himikat123/Weather-monitor-BIM32/display Nextion/img/background.png

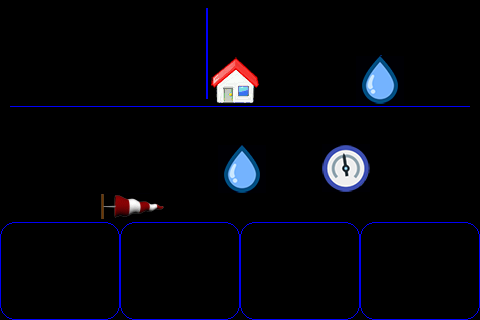
display Nextion/img/background.png
