himikat123/Weather-monitor-BIM32/display Nextion/img/clock.png

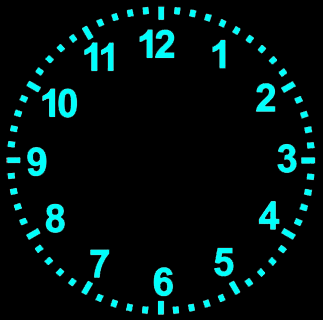
display Nextion/img/clock.png
