himikat123/Weather-monitor-BIM32/enclosure/BME680 enclosure/BME680_1.jpg

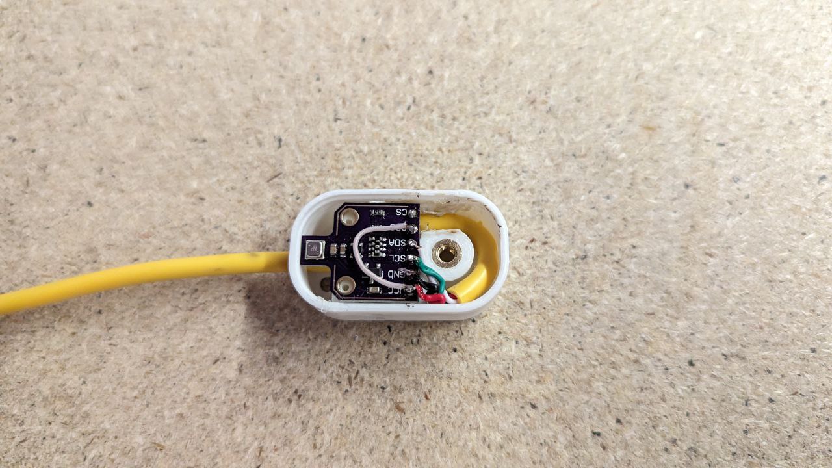
enclosure/BME680 enclosure/BME680_1.jpg
