himikat123/Weather-monitor-BIM32/enclosure/BME680 enclosure/STL/BME680_main.png

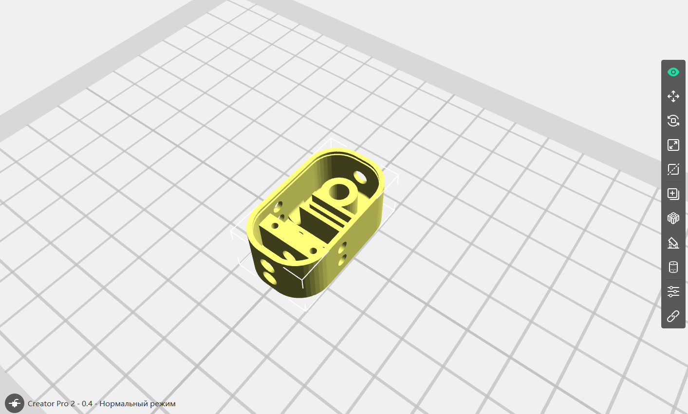
enclosure/BME680 enclosure/STL/BME680_main.png
