himikat123/Weather-monitor-BIM32/enclosure/Solidworks2023/buttons/alarm/alarm_button.png

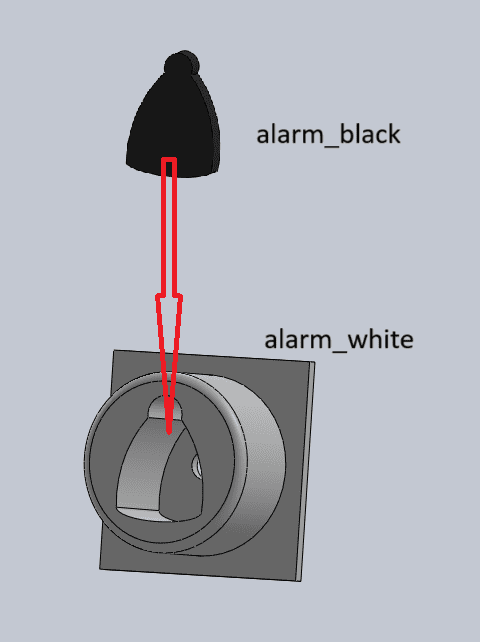
enclosure/Solidworks2023/buttons/alarm/alarm_button.png
