himikat123/Weather-monitor-BIM32/enclosure/Solidworks2023/buttons/display_1/disp1_button.png

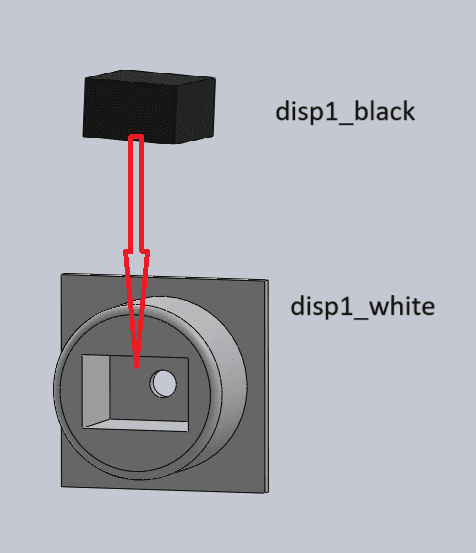
enclosure/Solidworks2023/buttons/display_1/disp1_button.png
