himikat123/Weather-monitor-BIM32/enclosure/Solidworks2023/buttons/display_2/disp2_button.png

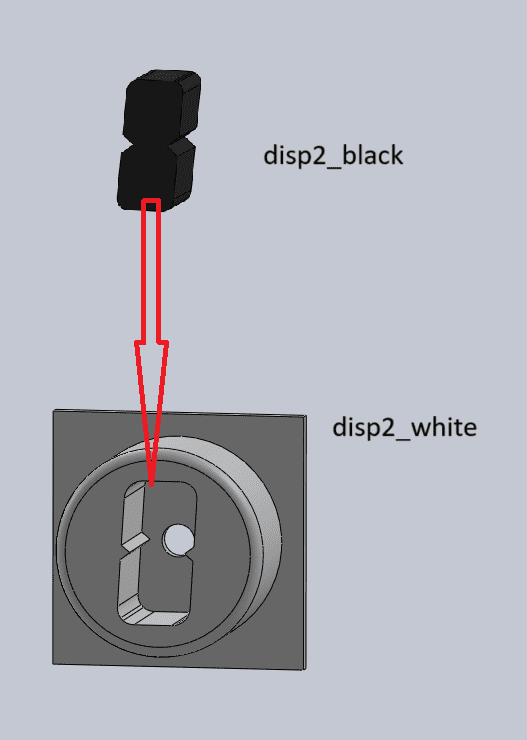
enclosure/Solidworks2023/buttons/display_2/disp2_button.png
