himikat123/Weather-monitor-BIM32/enclosure/Solidworks2023/buttons/reset/reset_button.png

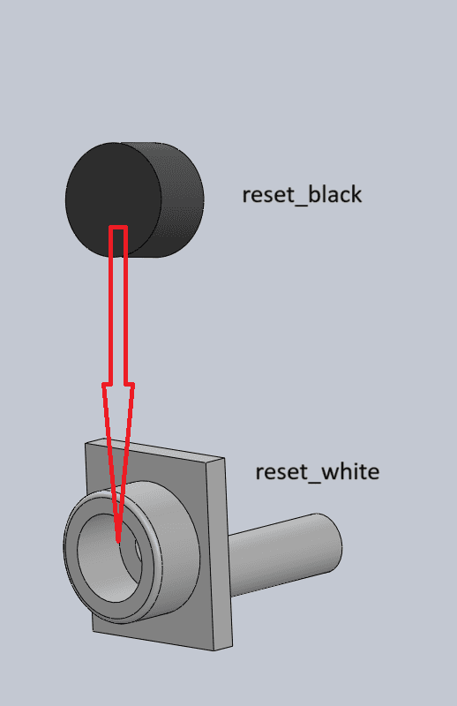
enclosure/Solidworks2023/buttons/reset/reset_button.png
