himikat123/Weather-monitor-BIM32/enclosure/Solidworks2023/buttons/settings/settings_button.png

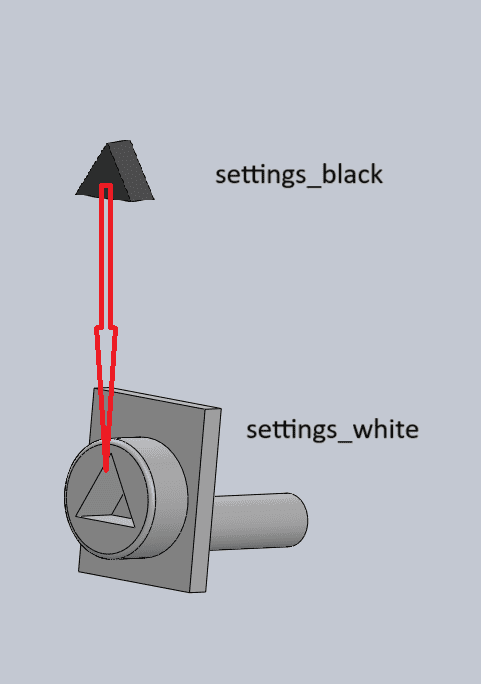
enclosure/Solidworks2023/buttons/settings/settings_button.png
