himikat123/Weather-monitor-BIM32/enclosure/Solidworks2023/clipSpeakerConnector.png

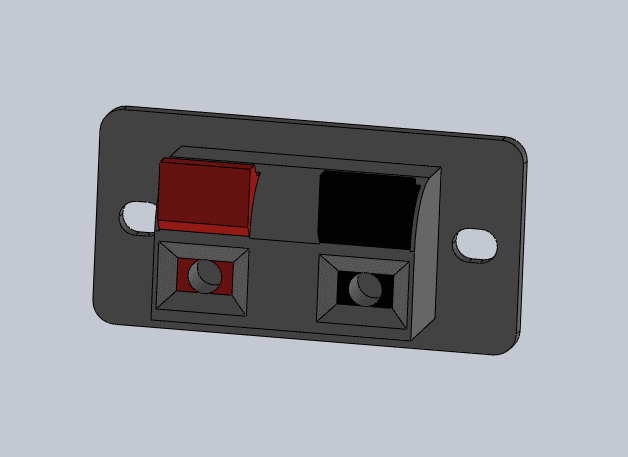
enclosure/Solidworks2023/clipSpeakerConnector.png
