himikat123/Weather-monitor-BIM32/enclosure/Solidworks2023/cover/cover.png

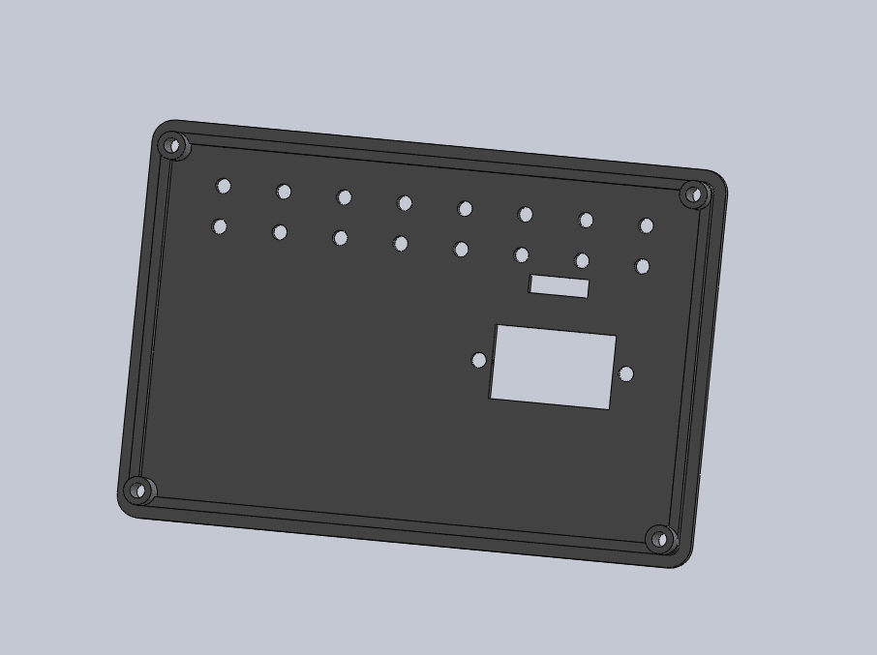
enclosure/Solidworks2023/cover/cover.png
