himikat123/Weather-monitor-BIM32/enclosure/Solidworks2023/display/display.png

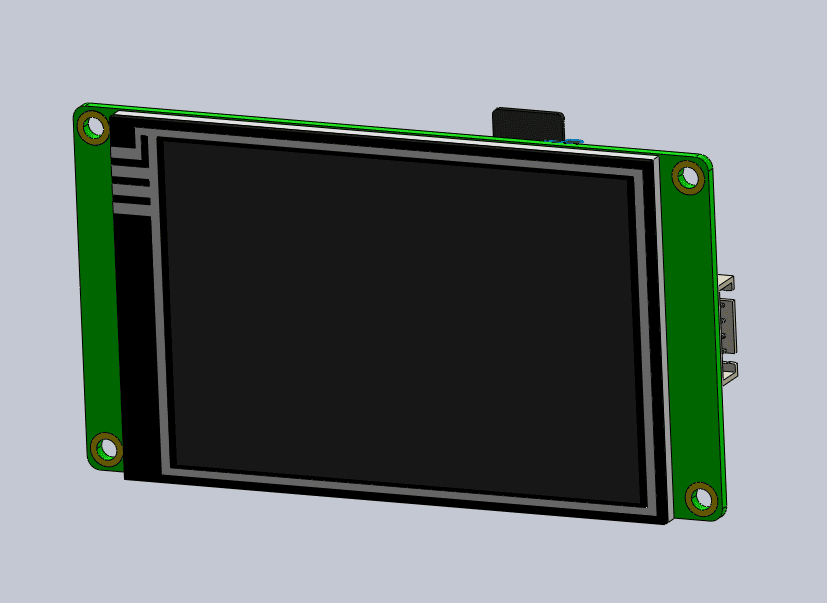
enclosure/Solidworks2023/display/display.png
