himikat123/Weather-monitor-BIM32/enclosure/Solidworks2023/face/face.png

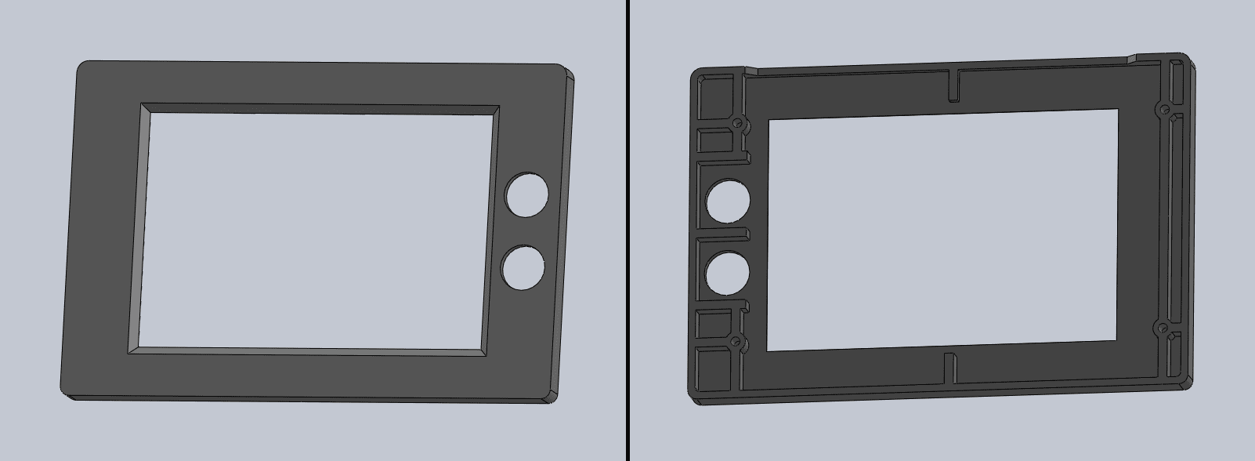
enclosure/Solidworks2023/face/face.png
