himikat123/Weather-monitor-BIM32/enclosure/Solidworks2023/frame/frame.png

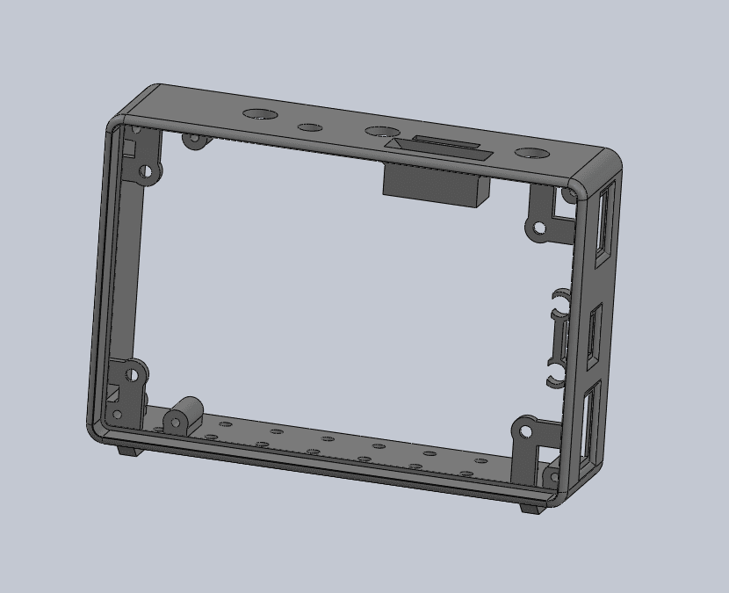
enclosure/Solidworks2023/frame/frame.png
