himikat123/Weather-monitor-BIM32/enclosure/Solidworks2023/lid/lid.png

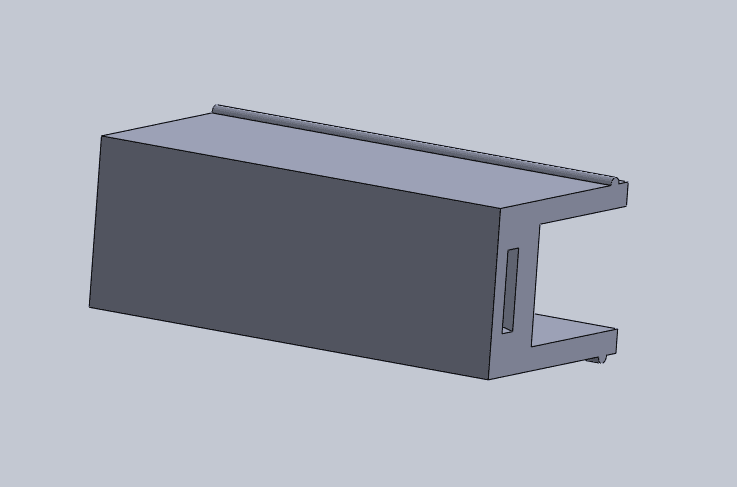
enclosure/Solidworks2023/lid/lid.png
