himikat123/Weather-monitor-BIM32/enclosure/Solidworks2023/pcb/pcb.png

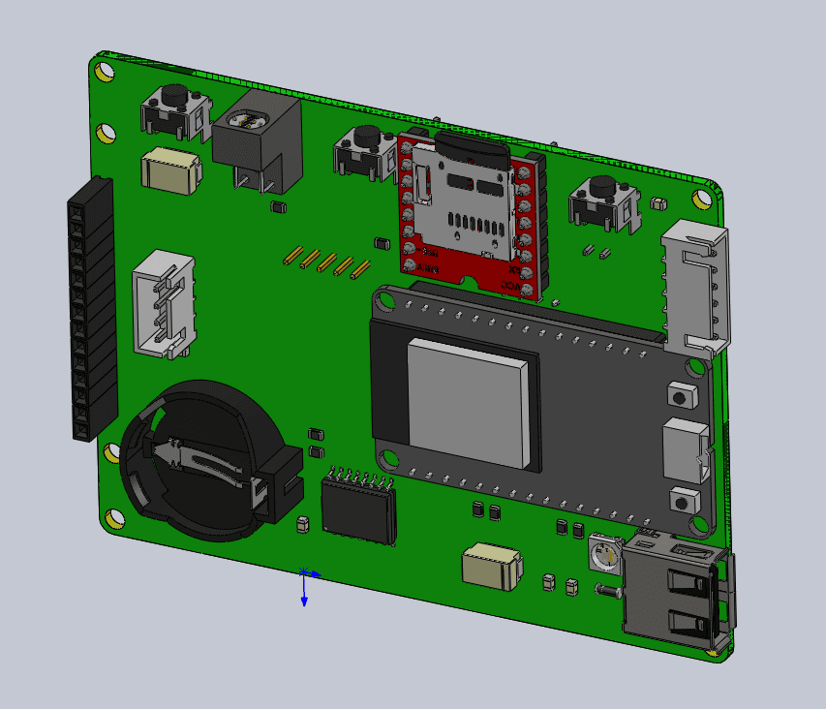
enclosure/Solidworks2023/pcb/pcb.png
