himikat123/Weather-monitor-BIM32/enclosure/Solidworks2023/photoresistor/photoresistor.png

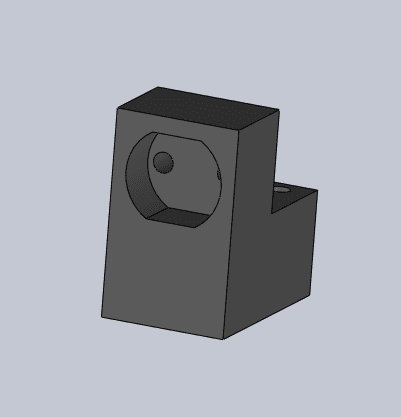
enclosure/Solidworks2023/photoresistor/photoresistor.png
