himikat123/Weather-monitor-BIM32/enclosure/Solidworks2023/screw1.png

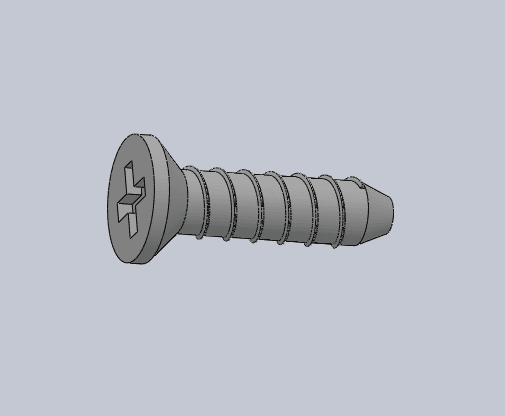
enclosure/Solidworks2023/screw1.png
