himikat123/Weather-monitor-BIM32/enclosure/Solidworks2023/screw2.png

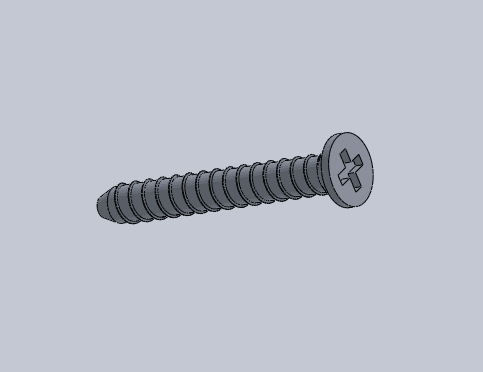
enclosure/Solidworks2023/screw2.png
