himikat123/Weather-monitor-BIM32/enclosure/Solidworks2023/speaker.png

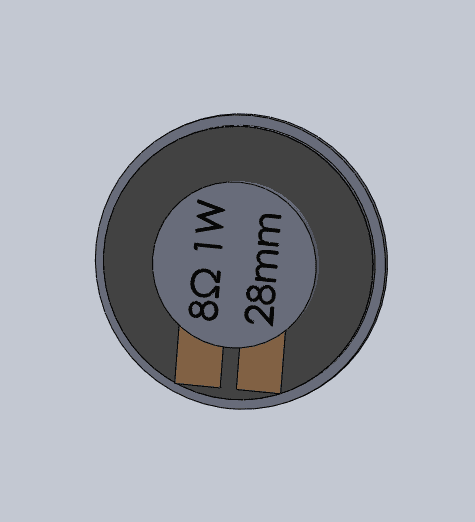
enclosure/Solidworks2023/speaker.png
