himikat123/Weather-monitor-BIM32/enclosure/STL/buttons/alarm/alarm_black.png

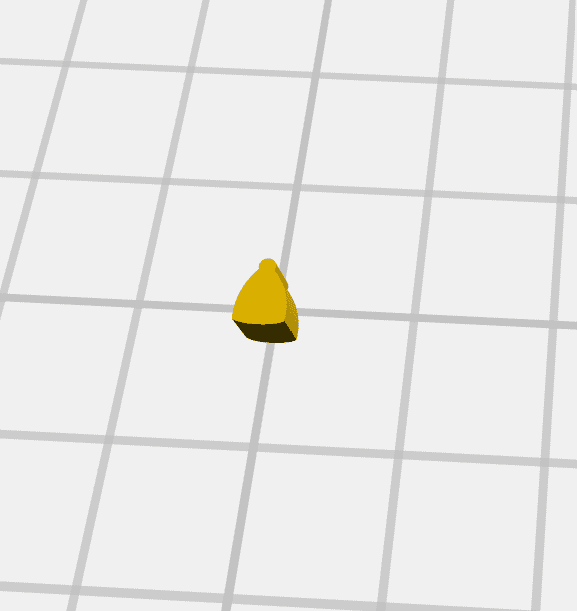
enclosure/STL/buttons/alarm/alarm_black.png
