himikat123/Weather-monitor-BIM32/enclosure/STL/buttons/alarm/alarm_white.png

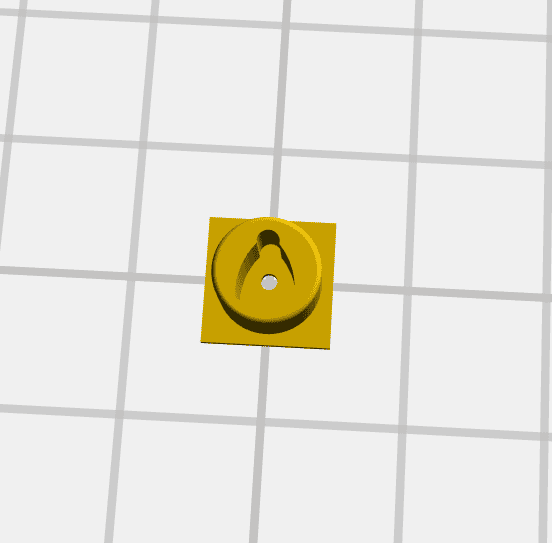
enclosure/STL/buttons/alarm/alarm_white.png
