himikat123/Weather-monitor-BIM32/enclosure/STL/buttons/display_1/disp1_black.png

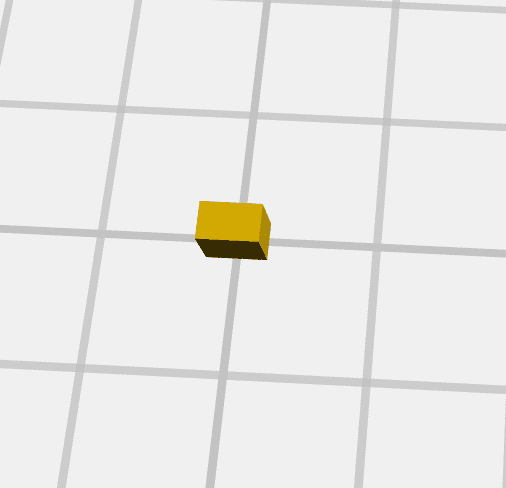
enclosure/STL/buttons/display_1/disp1_black.png
