himikat123/Weather-monitor-BIM32/enclosure/STL/buttons/display_2/disp2_black.png

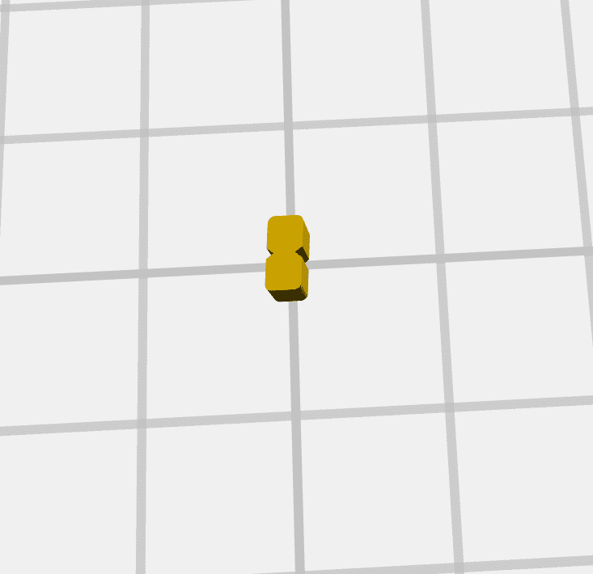
enclosure/STL/buttons/display_2/disp2_black.png
