himikat123/Weather-monitor-BIM32/enclosure/STL/buttons/reset/reset_black.png

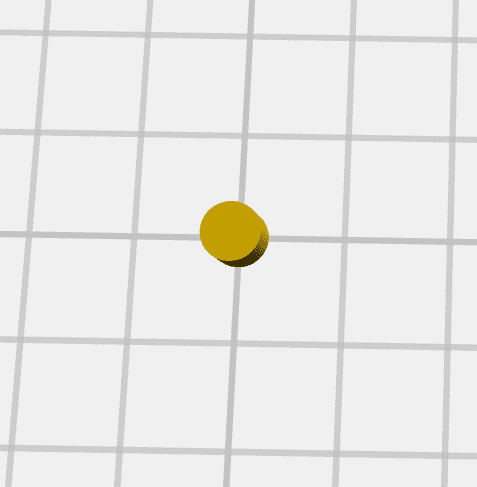
enclosure/STL/buttons/reset/reset_black.png
