himikat123/Weather-monitor-BIM32/enclosure/STL/buttons/reset/reset_white.png

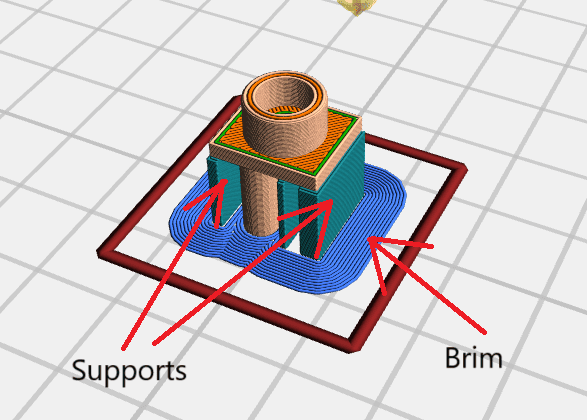
enclosure/STL/buttons/reset/reset_white.png
