himikat123/Weather-monitor-BIM32/enclosure/STL/buttons/settings/setiings_black.png

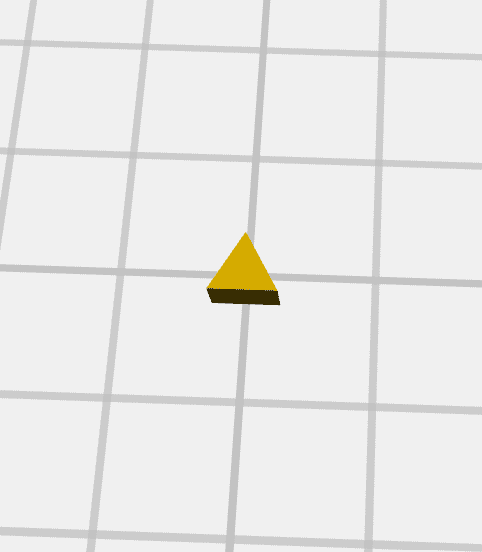
enclosure/STL/buttons/settings/setiings_black.png
