himikat123/Weather-monitor-BIM32/enclosure/STL/buttons/settings/setiings_white.png

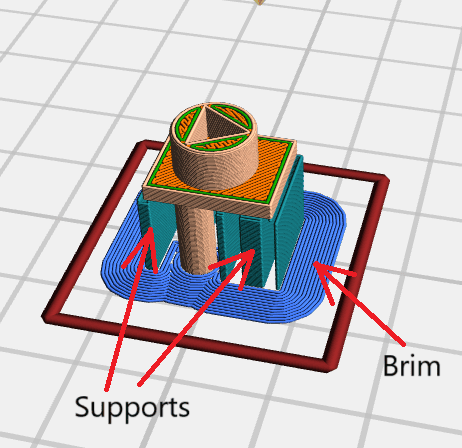
enclosure/STL/buttons/settings/setiings_white.png
