himikat123/Weather-monitor-BIM32/enclosure/STL/cover/cover_with_clip.png

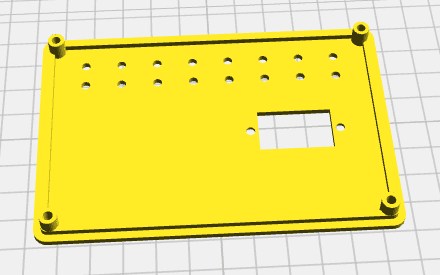
enclosure/STL/cover/cover_with_clip.png
