himikat123/Weather-monitor-BIM32/enclosure/STL/face/face.png

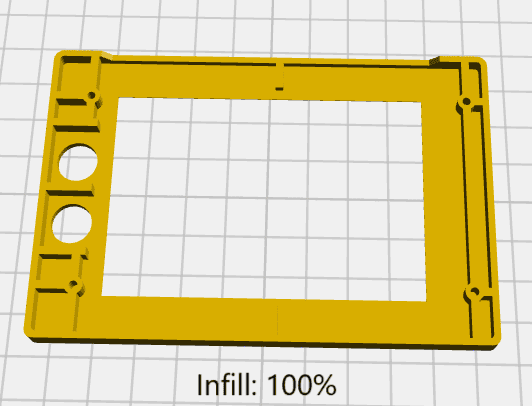
enclosure/STL/face/face.png
