himikat123/Weather-monitor-BIM32/enclosure/STL/face/face_wo_button_holes.png

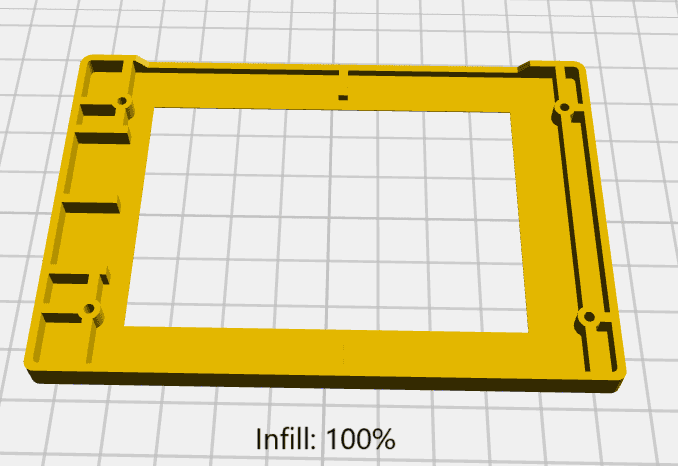
enclosure/STL/face/face_wo_button_holes.png
