himikat123/Weather-monitor-BIM32/enclosure/STL/frame/frame.png

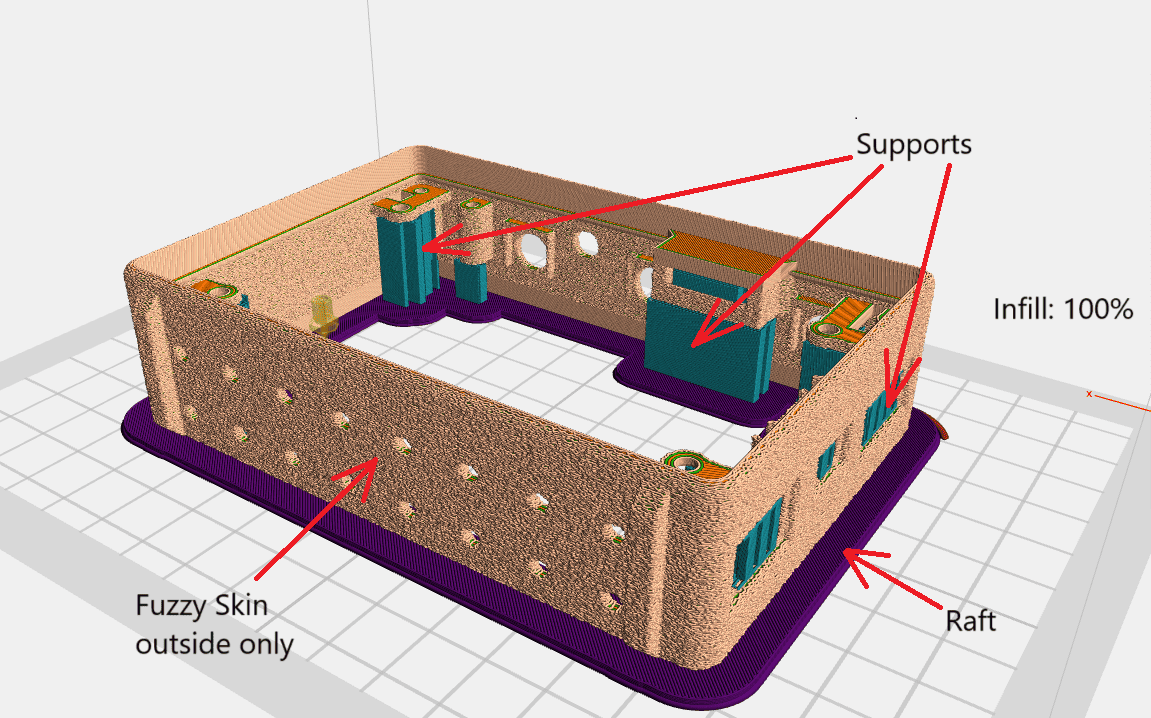
enclosure/STL/frame/frame.png
