himikat123/Weather-monitor-BIM32/enclosure/STL/frame/frame_with_4_pin_sensors_connector.png

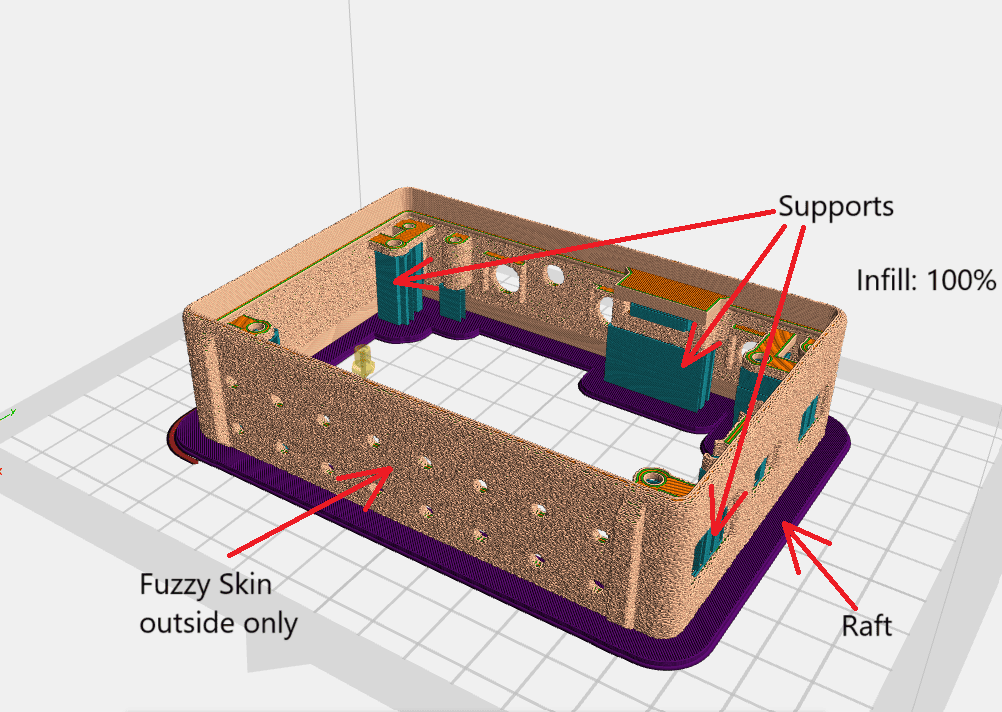
enclosure/STL/frame/frame_with_4_pin_sensors_connector.png
