himikat123/Weather-monitor-BIM32/enclosure/STL/frame/frame_wo_light_sensor_hole.png

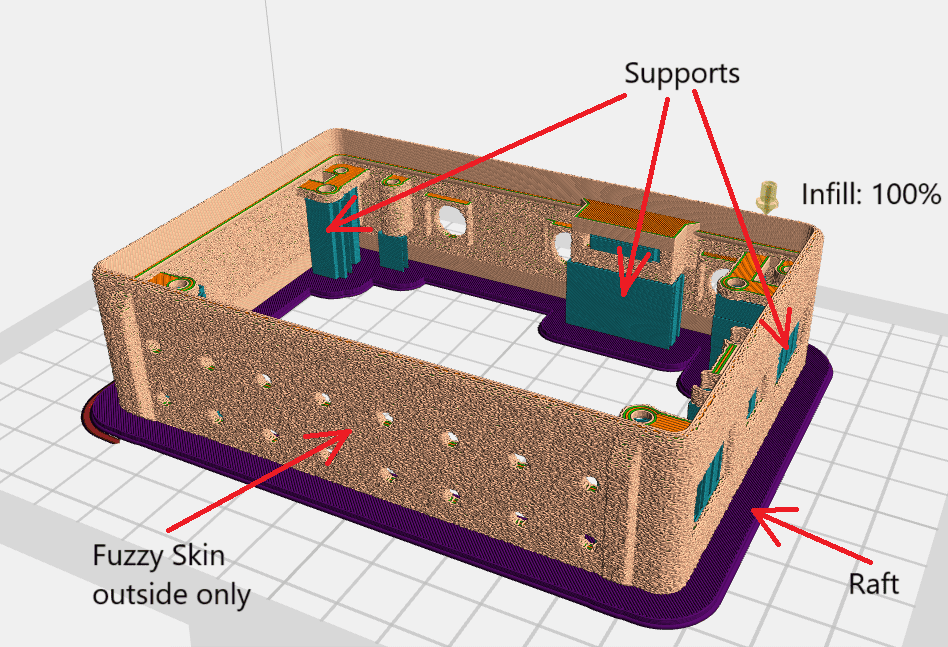
enclosure/STL/frame/frame_wo_light_sensor_hole.png
