himikat123/Weather-monitor-BIM32/enclosure/STL/frame/frame_wo_top_buttons_holes.png

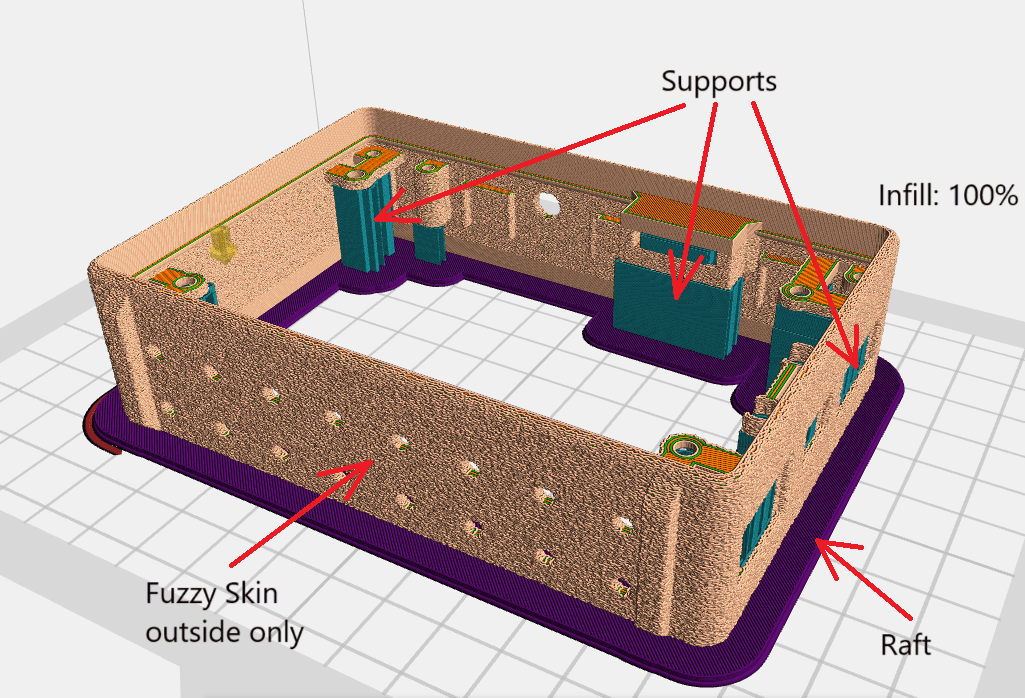
enclosure/STL/frame/frame_wo_top_buttons_holes.png
