himikat123/Weather-monitor-BIM32/enclosure/STL/lid/lid.png

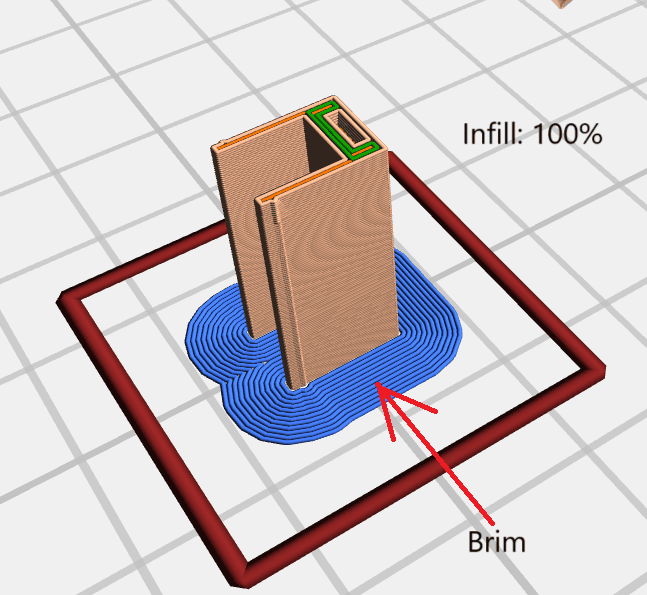
enclosure/STL/lid/lid.png
