himikat123/Weather-monitor-BIM32/enclosure/STL/photoresistor/photoresistor.png

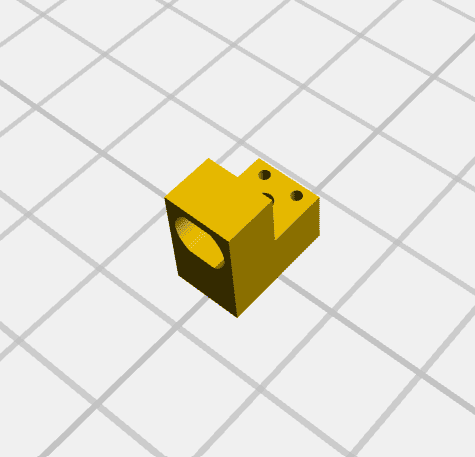
enclosure/STL/photoresistor/photoresistor.png
