himikat123/Weather-monitor-BIM32/img/aboutRU.png

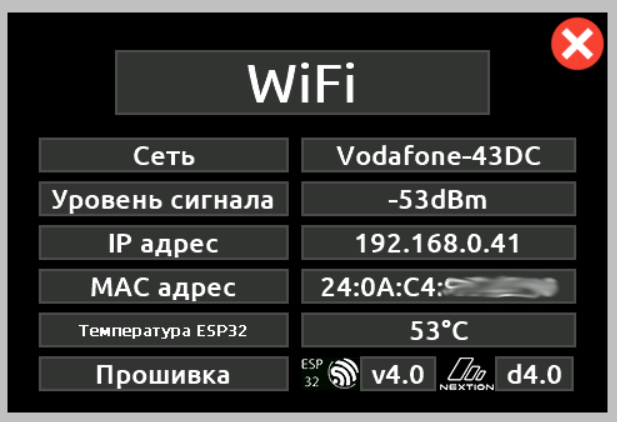
img/aboutRU.png
