himikat123/Weather-monitor-BIM32/img/device1_RU.jpg

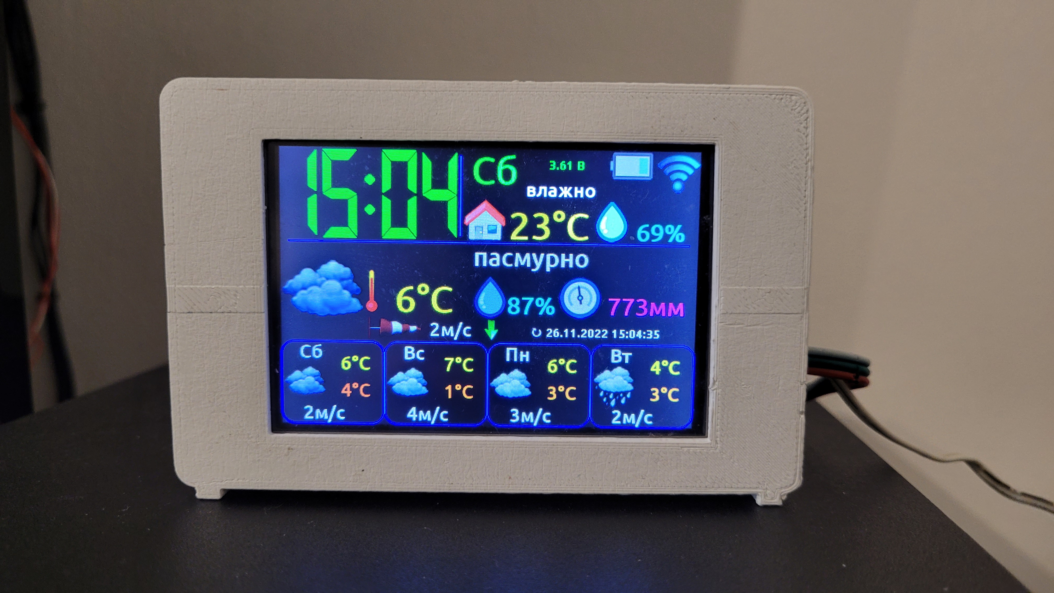
img/device1_RU.jpg
