himikat123/Weather-monitor-BIM32/img/f6_ru.jpg

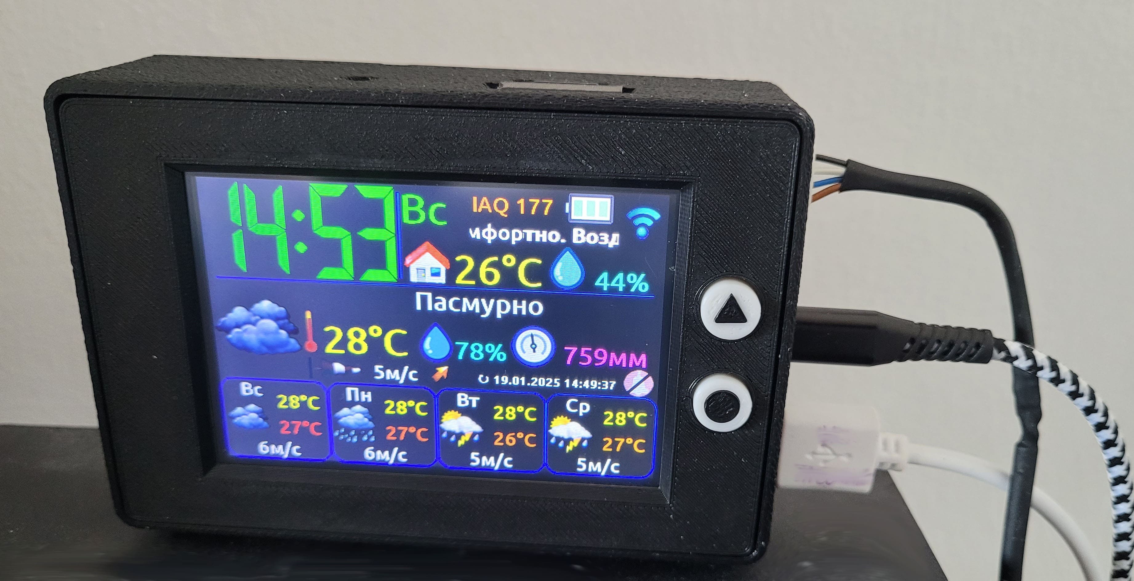
img/f6_ru.jpg
