himikat123/Weather-monitor-BIM32/img/mainRU.gif

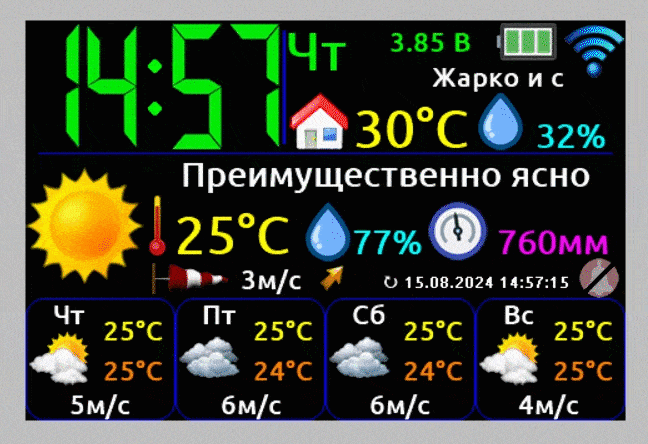
img/mainRU.gif
