himikat123/Weather-monitor-BIM32/PCB/diptrace/BIM32.png

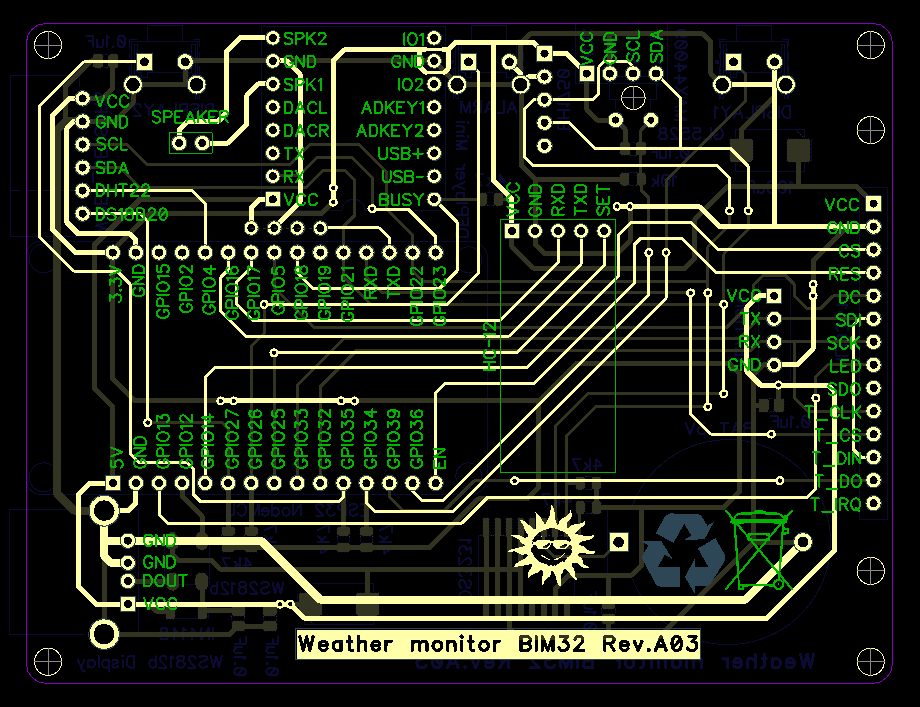
PCB/diptrace/BIM32.png
