himikat123/Weather-monitor-BIM32/PCB/diptrace/Version.png

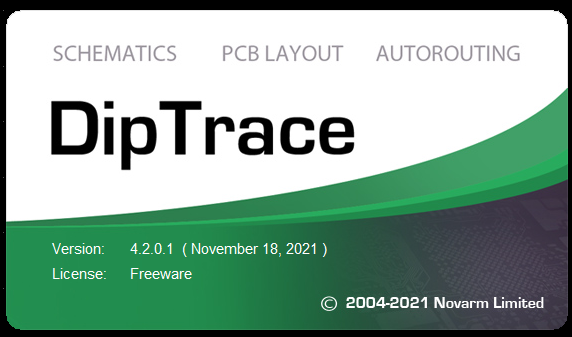
PCB/diptrace/Version.png
