himikat123/Weather-monitor-BIM32/PCB/PCB Bottom.png

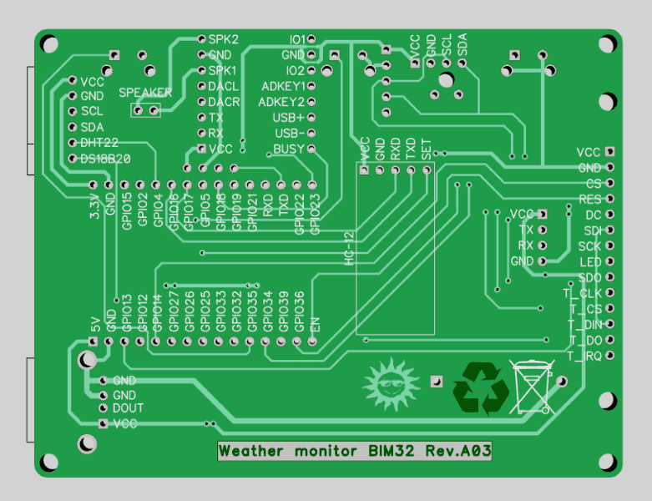
PCB/PCB Bottom.png
