himikat123/Weather-monitor-BIM32/PCB/PCB Top.png

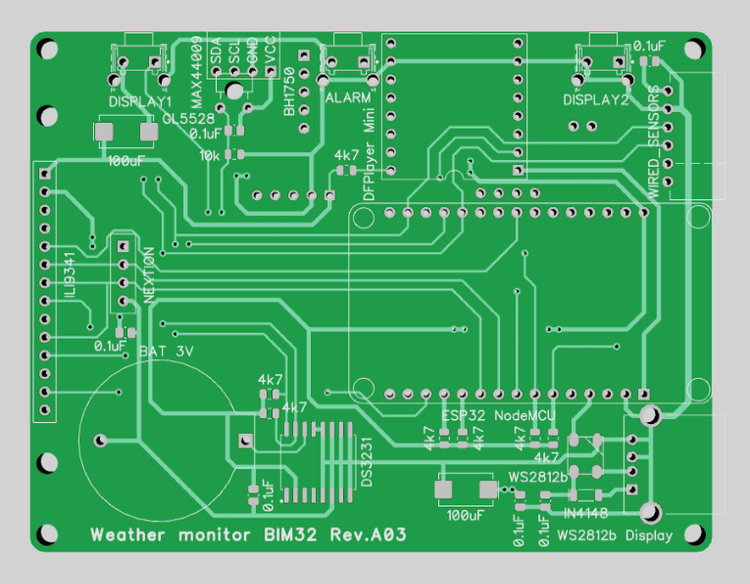
PCB/PCB Top.png
