himikat123/Weather-monitor-BIM32/PCB/sprint layout/BIM32.png

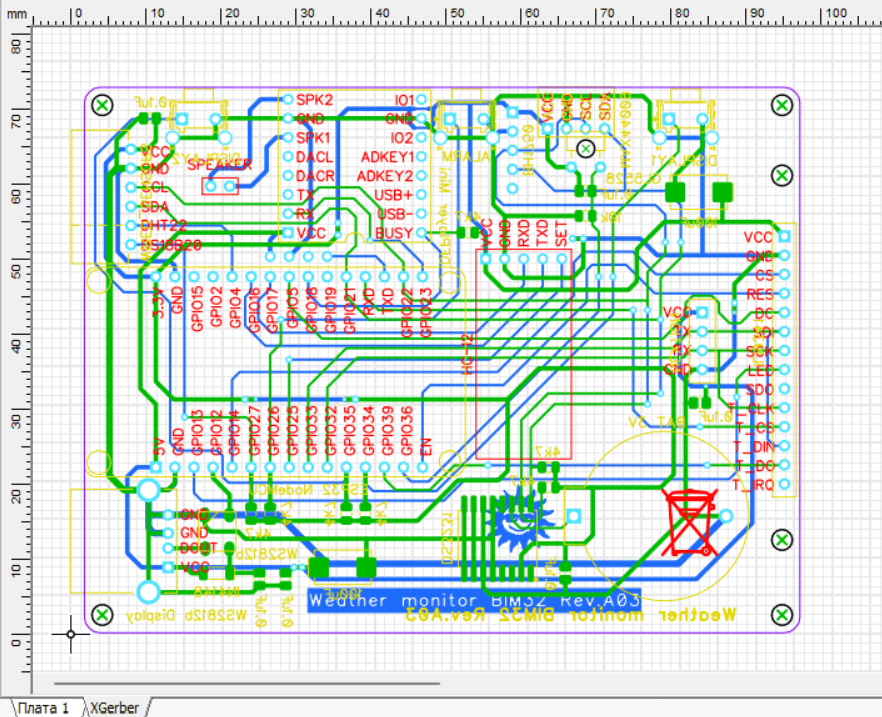
PCB/sprint layout/BIM32.png
