himikat123/Weather-monitor-BIM32/img/components/bh1750.png

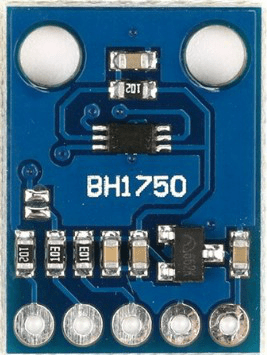
img/components/bh1750.png
