himikat123/Weather-monitor-BIM32/img/components/bme680.png

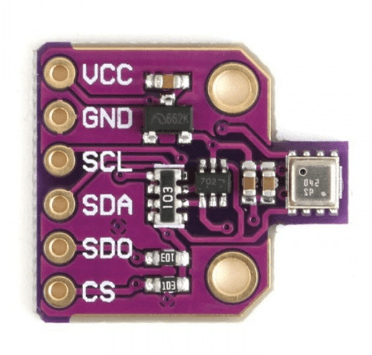
img/components/bme680.png
