himikat123/Weather-monitor-BIM32/img/components/bmp180.png

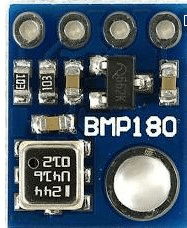
img/components/bmp180.png
