himikat123/Weather-monitor-BIM32/img/components/dht22.png

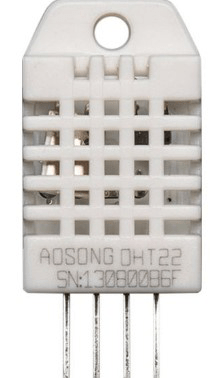
img/components/dht22.png
