himikat123/Weather-monitor-BIM32/img/components/ds3231.png

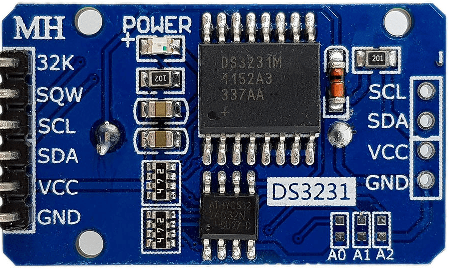
img/components/ds3231.png
