himikat123/Weather-monitor-BIM32/img/components/esp32.png

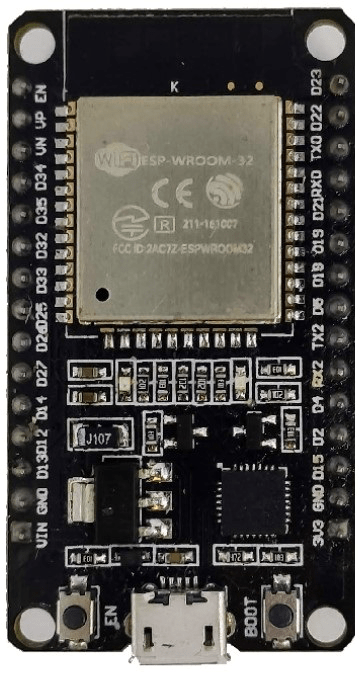
img/components/esp32.png
