himikat123/Weather-monitor-BIM32/img/components/hc-12.png

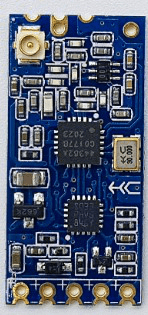
img/components/hc-12.png
