himikat123/Weather-monitor-BIM32/img/components/ili9341.png

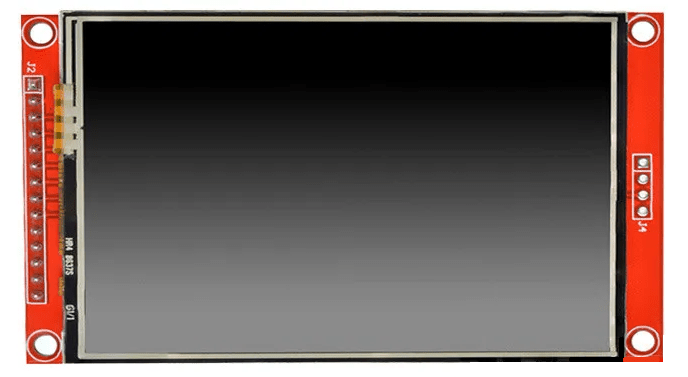
img/components/ili9341.png
