himikat123/Weather-monitor-BIM32/img/components/max44009.png

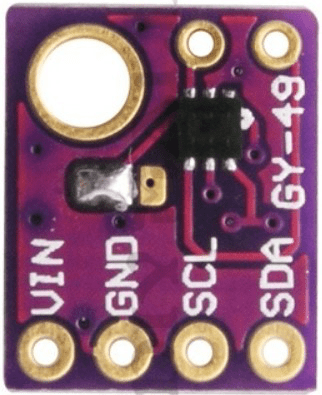
img/components/max44009.png
