himikat123/Weather-monitor-BIM32/img/components/photoresistor.png

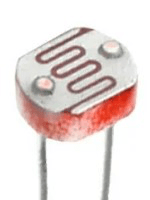
img/components/photoresistor.png
