himikat123/Weather-monitor-BIM32/img/components/ws2812b.png

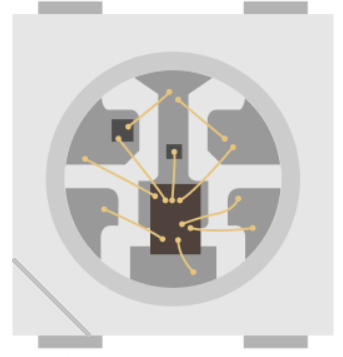
img/components/ws2812b.png
