himikat123/Weather-monitor-BIM32/enclosure/Solidworks2023/photoresistor/photoresistor.SLDPRT

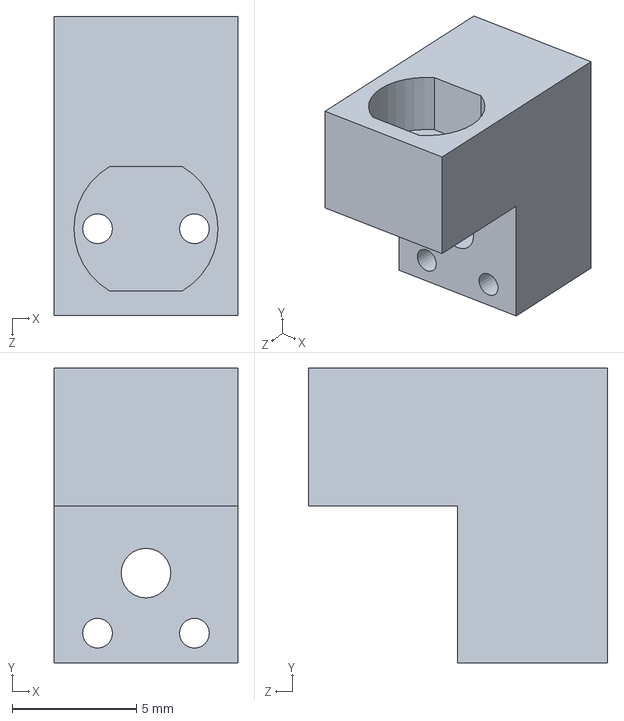
[picture p110: CAD file, 2025-01-19]
enclosure/Solidworks2023/photoresistor/photoresistor.SLDPRT
7.40 x 11.9 x 12.1 mm
