himikat123/Weather-monitor-BIM32/enclosure/STL/buttons/display_2/disp2_black.STL

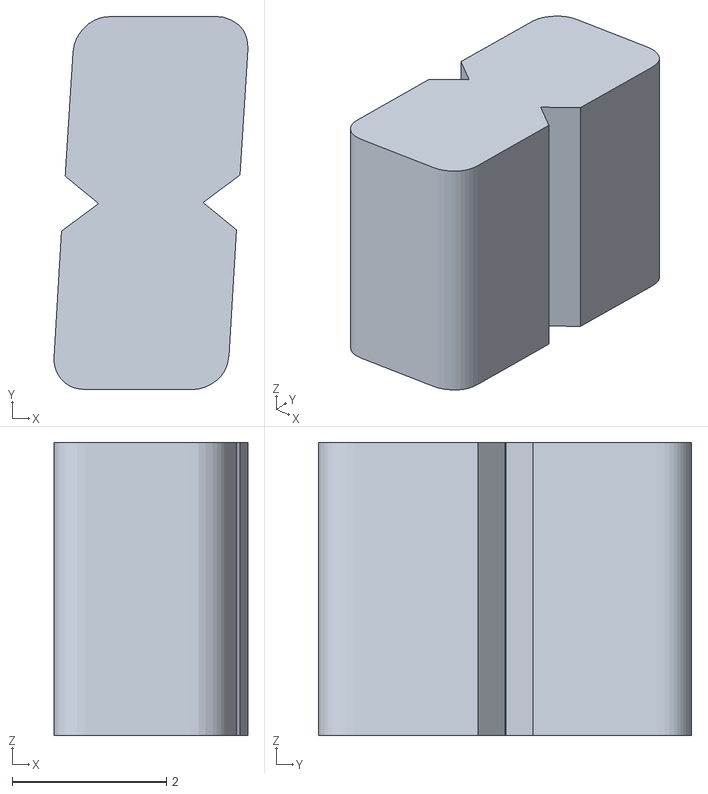
[picture p111: CAD file, 2025-01-19]
enclosure/STL/buttons/display_2/disp2_black.STL
2.51 x 4.84 x 3.80
