himikat123/Weather-monitor-BIM32/enclosure/STL/buttons/settings/setiings_white.STL

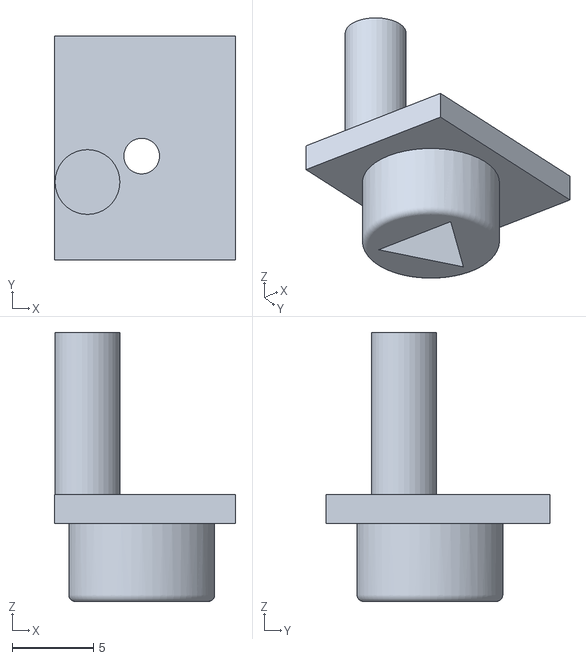
[picture p112: CAD file, 2025-01-19]
enclosure/STL/buttons/settings/setiings_white.STL
11.2 x 13.8 x 16.6
