himikat123/Weather-monitor-BIM32/enclosure/STL/cover/cover_with_speaker.STL

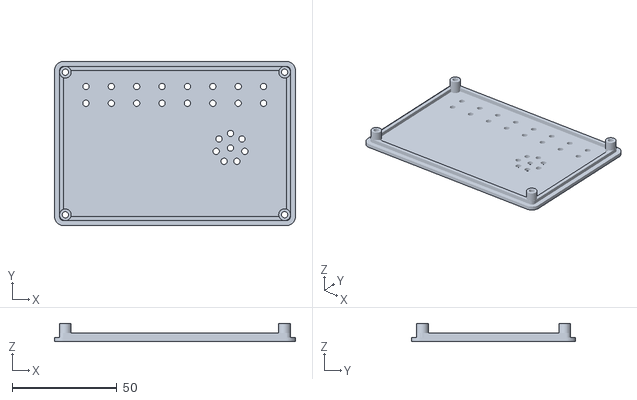
[picture p113: CAD file, 2025-01-19]
enclosure/STL/cover/cover_with_speaker.STL
114.9 x 78.4 x 8.60
