himikat123/Weather-monitor-BIM32/PCB/diptrace/3d models/JST - XH - Thru (V) - 4Pin - 2.54mm.stp

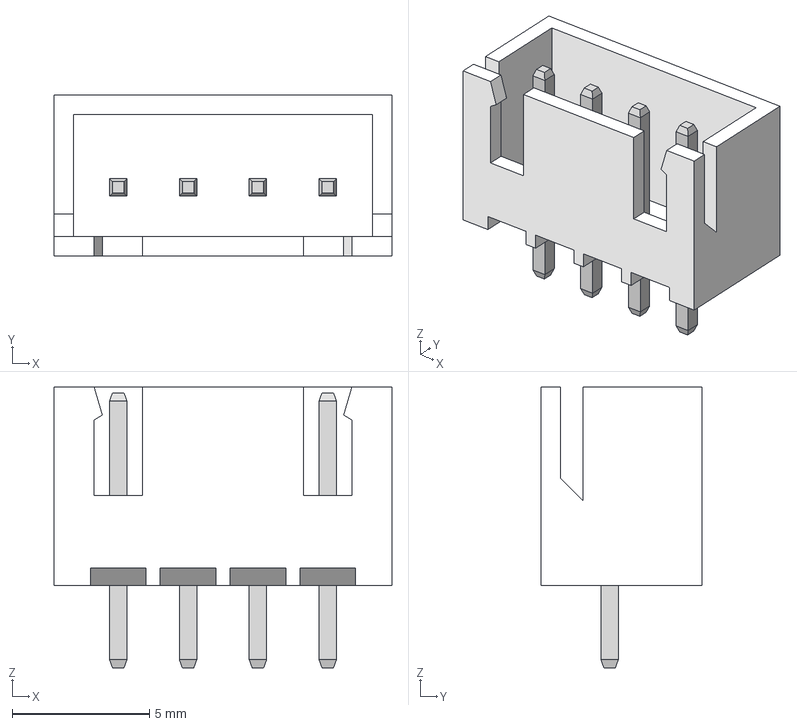
[picture p114: CAD file, 2025-01-19]
PCB/diptrace/3d models/JST - XH - Thru (V) - 4Pin - 2.54mm.stp
12.3 x 5.84 x 10.2 mm
