himikat123/Weather-monitor-BIM32/enclosure/BME680 enclosure/STL/cover for 2 color print/BME680_cover_white.STL

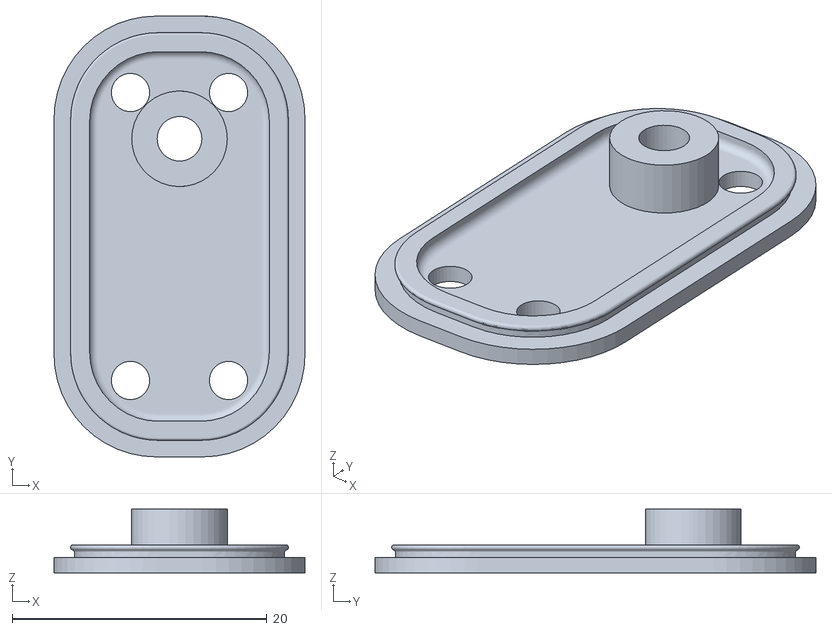
[picture p115: CAD file, 2024-01-01]
enclosure/BME680 enclosure/STL/cover for 2 color print/BME680_cover_white.STL
19.7 x 34.6 x 5.00
