himikat123/Weather-monitor-BIM32/enclosure/Solidworks2023/buttons/reset/reset_black.SLDPRT

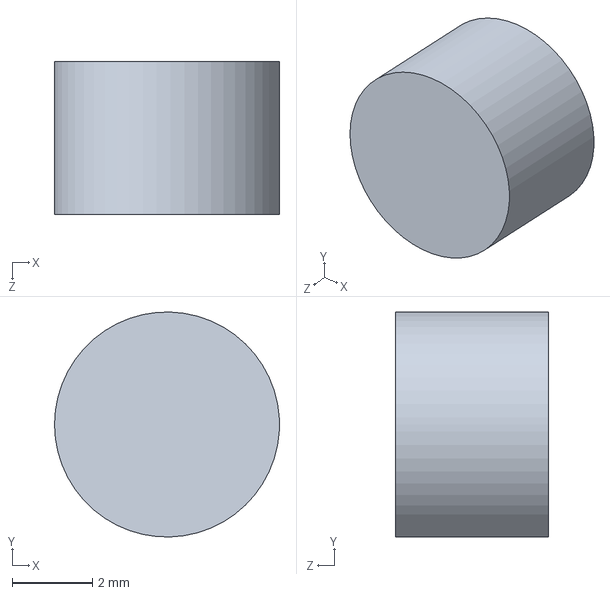
[picture p116: CAD file, 2025-01-19]
enclosure/Solidworks2023/buttons/reset/reset_black.SLDPRT
5.60 x 5.60 x 3.80 mm
