himikat123/Weather-monitor-BIM32/enclosure/Solidworks2023/clipSpeakerConnector.SLDPRT

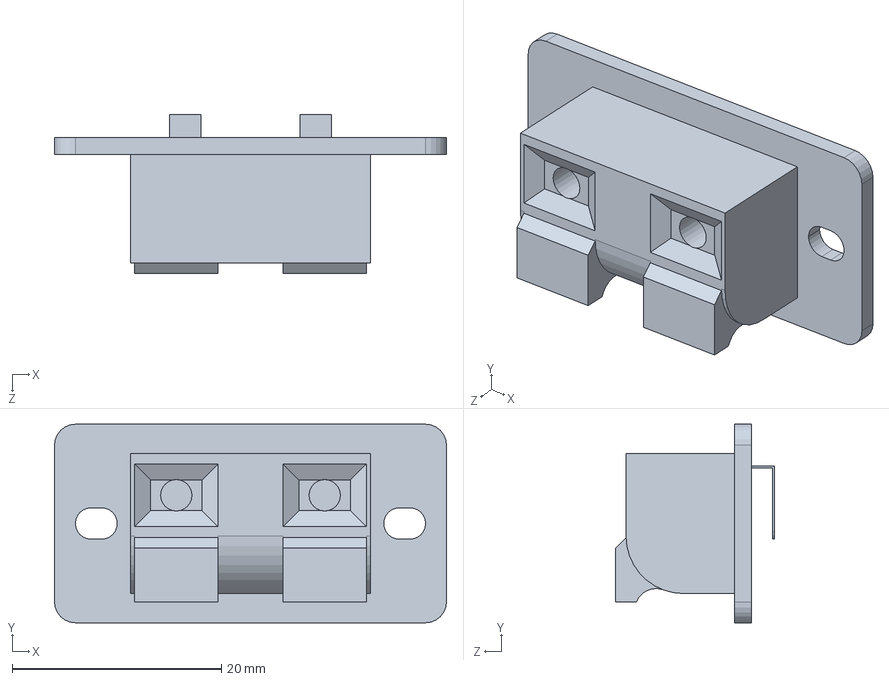
[picture p117: CAD file, 2025-01-19]
enclosure/Solidworks2023/clipSpeakerConnector.SLDPRT
37.5 x 19.0 x 15.2 mm
