himikat123/Weather-monitor-BIM32/PCB/diptrace/3d models/JST - XH - Thru (R) - 2Pin - 2.54mm.stp

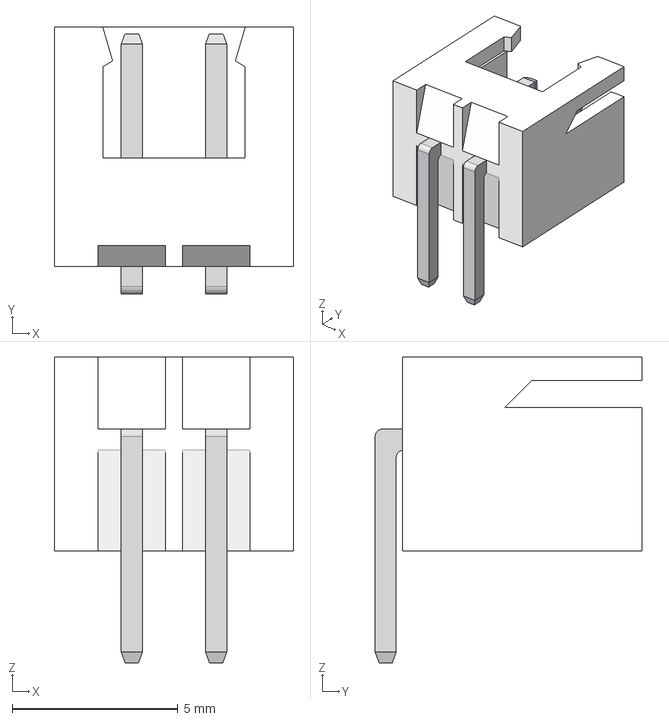
[picture p118: CAD file, 2025-01-19]
PCB/diptrace/3d models/JST - XH - Thru (R) - 2Pin - 2.54mm.stp
7.21 x 8.04 x 9.22 mm
