himikat123/Weather-monitor-BIM32/enclosure/BME680 enclosure/SOLIDWORKS 2023/CJMCU-680.SLDPRT

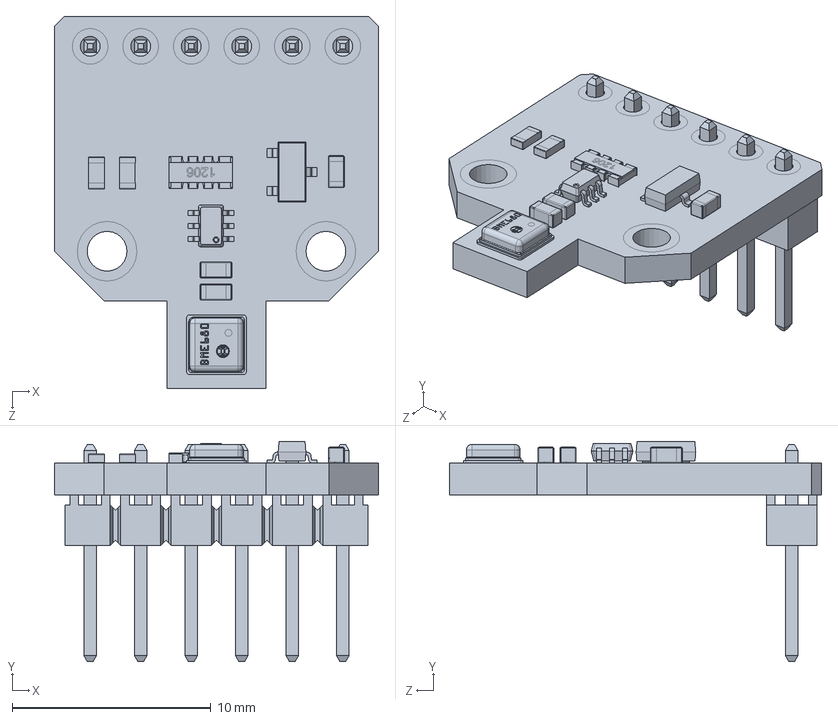
[picture p119: CAD file, 2024-01-01]
enclosure/BME680 enclosure/SOLIDWORKS 2023/CJMCU-680.SLDPRT
16.3 x 11.1 x 18.7 mm
