himikat123/Weather-monitor-BIM32/enclosure/Solidworks2023/speaker.SLDPRT

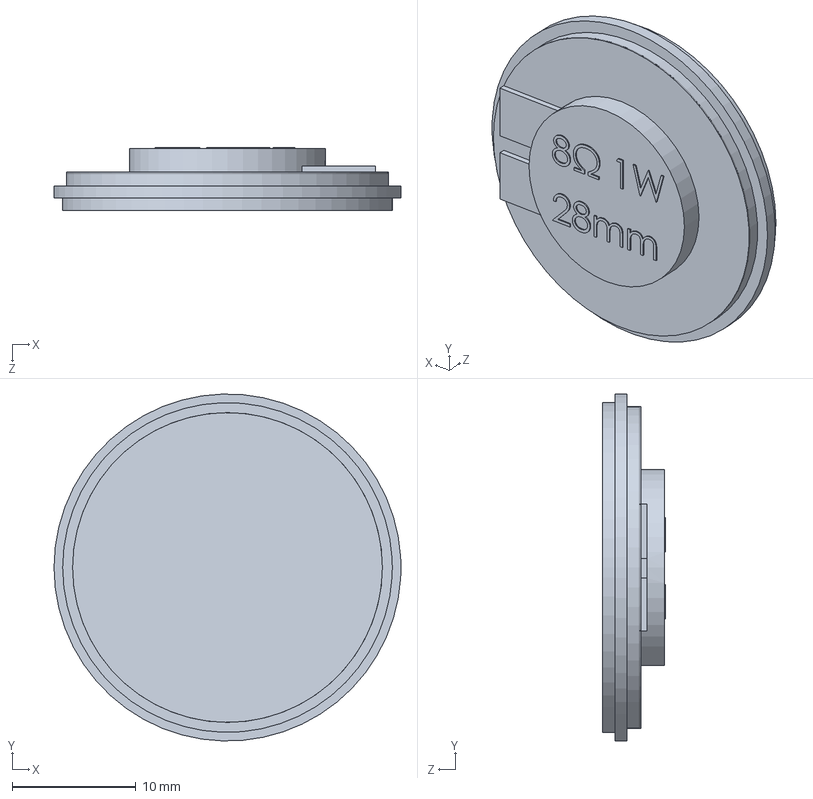
[picture p120: CAD file, 2024-08-18]
enclosure/Solidworks2023/speaker.SLDPRT
28.0 x 28.0 x 5.10 mm
