himikat123/Weather-monitor-BIM32/PCB/diptrace/3d models/ILI9341_3_2.step

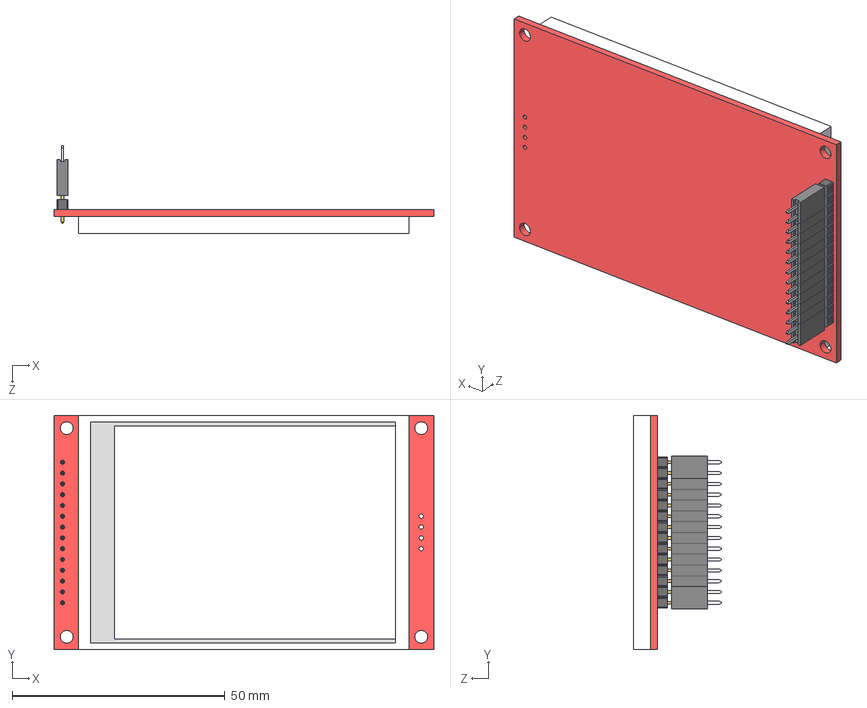
[picture p121: CAD file, 2024-08-15]
PCB/diptrace/3d models/ILI9341_3_2.step
89.3 x 55.0 x 20.6 mm
14-Pin Header - Male - 2.54mm_1.step.step_Standard
screen.step_Standard
disp_frame.step_Standard
touch.step_Standard
display_board.step_Standard
hdrf-1x14t_2.54_36x3_1.step_Standard
