himikat123/Weather-monitor-BIM32/PCB/diptrace/3d models/HC-12.STEP

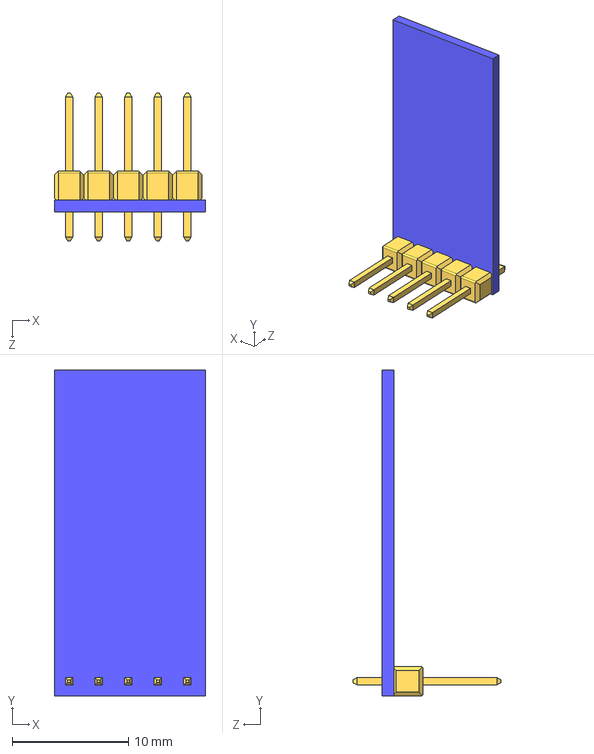
[picture p122: CAD file, 2024-08-15]
PCB/diptrace/3d models/HC-12.STEP
13.0 x 28.0 x 12.7 mm
hc12pcb___ _________.STEP_Standard
Pin Header 1x5 TH Pitch 2.54mm___ _________.STEP_Standard
