himikat123/Weather-monitor-BIM32/PCB/diptrace/3d models/BH-642_Battery_holder.STEP

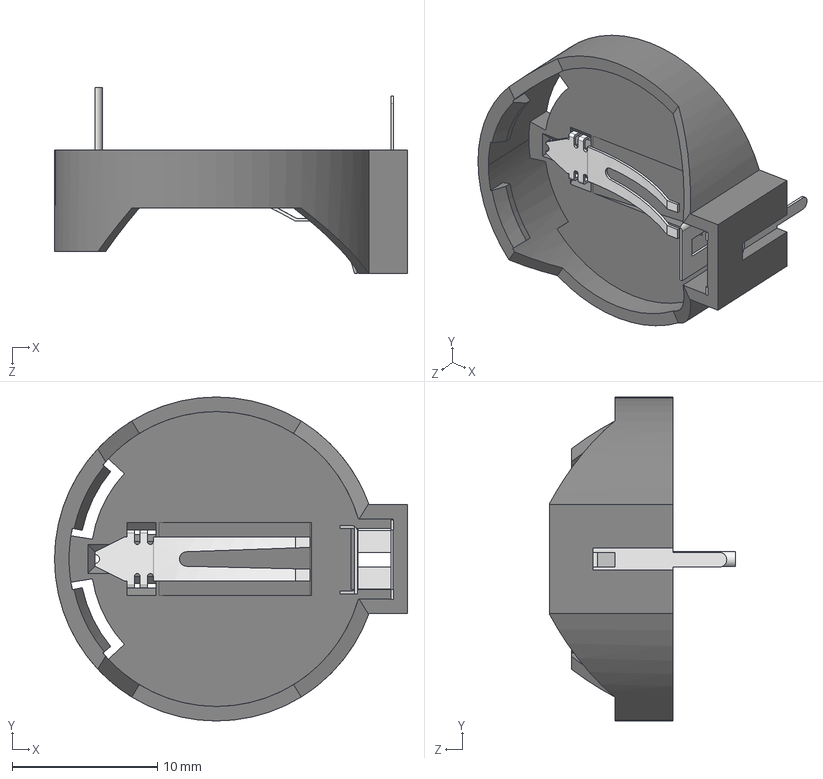
[picture p123: CAD file, 2024-08-15]
PCB/diptrace/3d models/BH-642_Battery_holder.STEP
24.3 x 22.3 x 12.8 mm
BH-642_Plastic
BH-642_Metal_minus
BH-642_Metal_plus
