himikat123/Weather-monitor-BIM32/PCB/diptrace/3d models/USB Connector Type A female.STEP

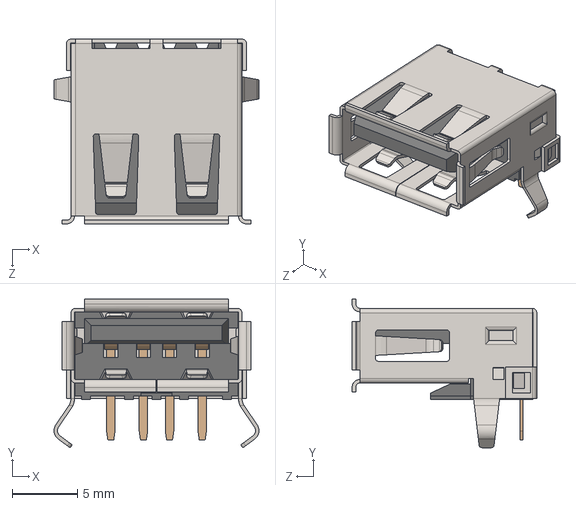
[picture p124: CAD file, 2024-08-15]
PCB/diptrace/3d models/USB Connector Type A female.STEP
15.7 x 11.4 x 14.1 mm
