himikat123/Weather-monitor-BIM32/PCB/diptrace/3d models/esp32.STEP

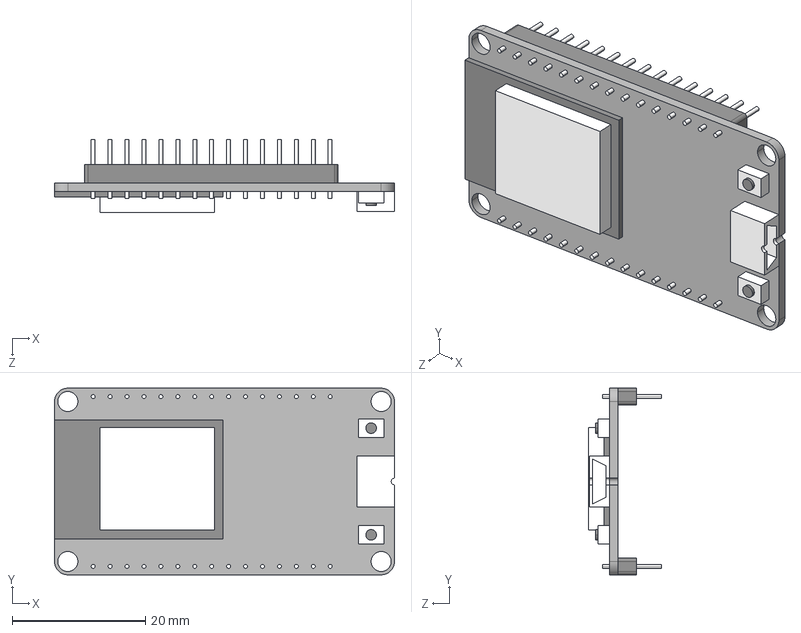
[picture p125: CAD file, 2024-08-15]
PCB/diptrace/3d models/esp32.STEP
51.0 x 28.0 x 10.9 mm
pcb_Standard
esp1_Standard
esp2_Standard
btn1_Standard x 2
btn2_Standard x 2
usb_Standard
dip_Standard x 2
pin_Standard x 2
