himikat123/Weather-monitor-BIM32/PCB/diptrace/3d models/gl5528.STEP

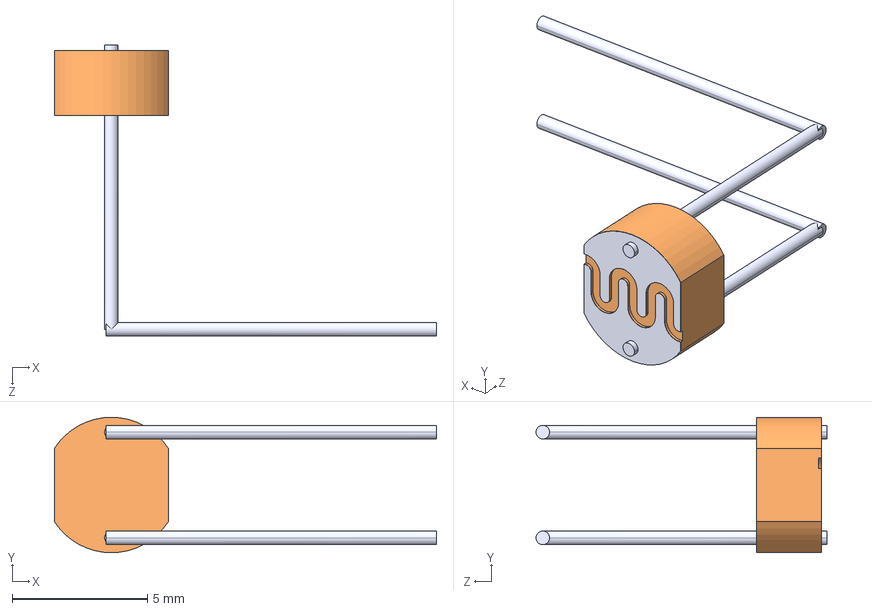
[picture p126: CAD file, 2024-08-15]
PCB/diptrace/3d models/gl5528.STEP
14.1 x 5.00 x 10.7 mm
sensor_Standard
cover_Standard
pin_Standard x 2
