himikat123/Weather-monitor-BIM32/PCB/diptrace/3d models/JST - XH - Thru (R) - 6Pin - 2.54mm.stp

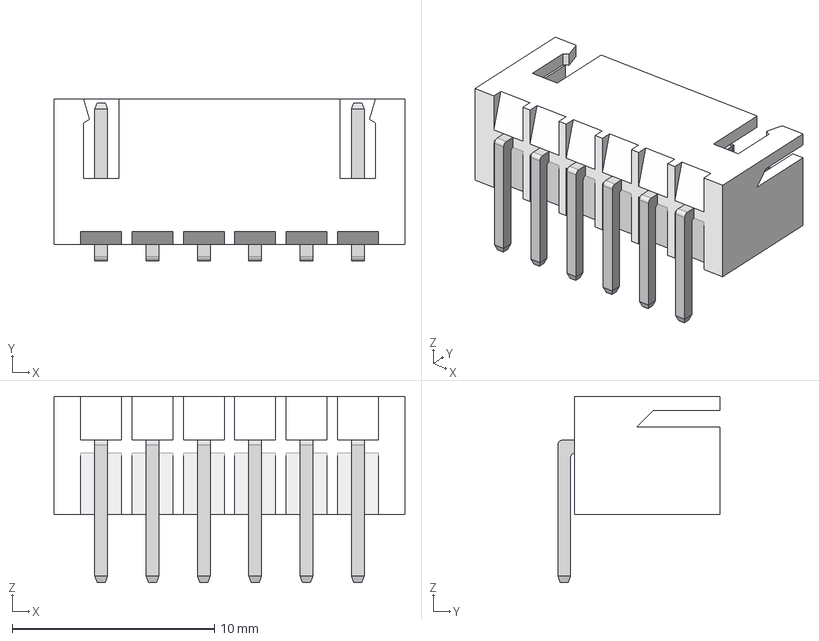
[picture p127: CAD file, 2024-08-15]
PCB/diptrace/3d models/JST - XH - Thru (R) - 6Pin - 2.54mm.stp
17.4 x 8.04 x 9.22 mm
