himikat123/Weather-monitor-BIM32/PCB/diptrace/3d models/bh1750_90deg.STEP

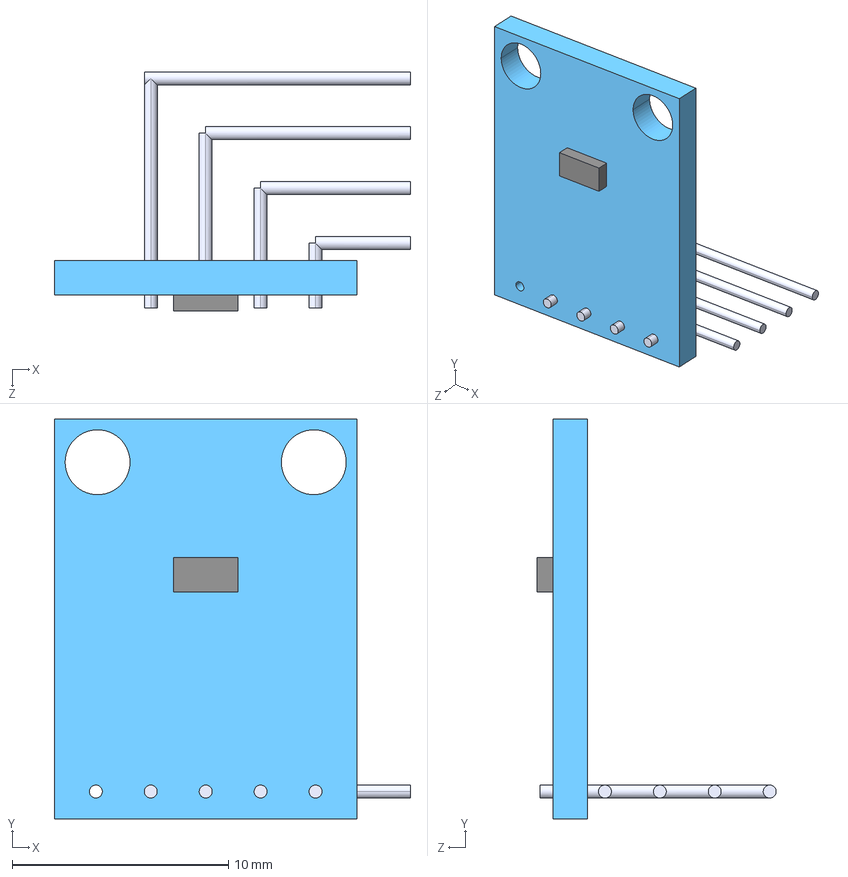
[picture p128: CAD file, 2024-08-15]
PCB/diptrace/3d models/bh1750_90deg.STEP
16.5 x 18.5 x 11.1 mm
pcb_Standard
sensor_Standard
pin90_Standard
