himikat123/Weather-monitor-BIM32/PCB/diptrace/3d models/WS2812B.step

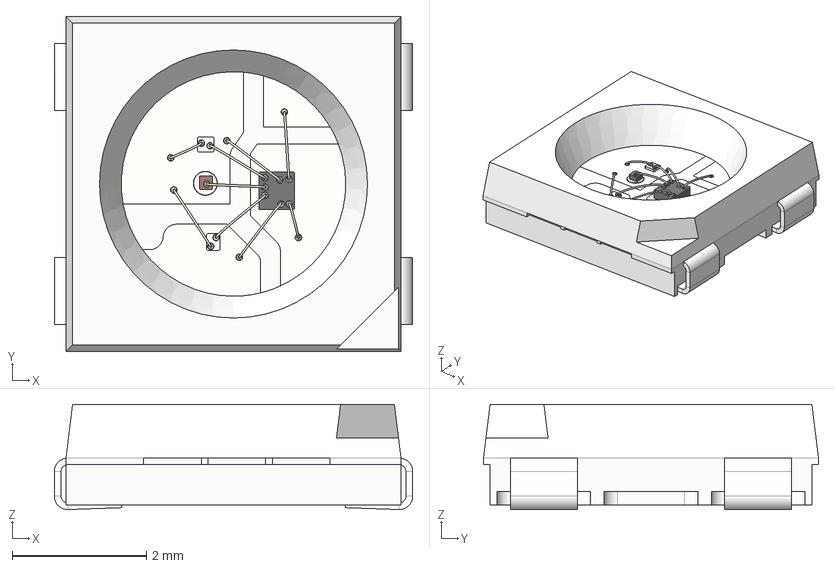
[picture p129: CAD file, 2022-12-17]
PCB/diptrace/3d models/WS2812B.step
5.35 x 5.00 x 1.57 mm
