himikat123/Weather-monitor-BIM32/PCB/diptrace/3d models/button.step

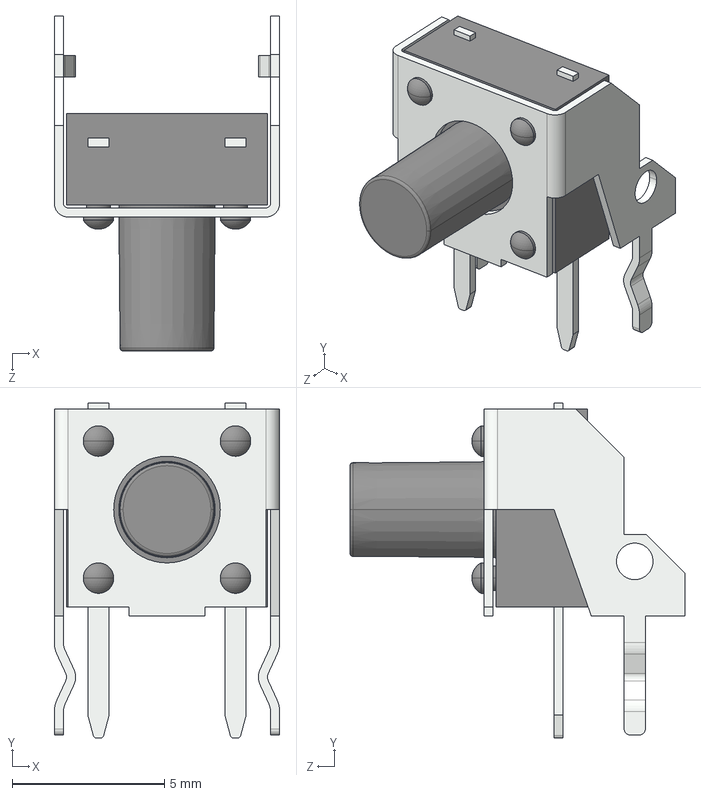
[picture p130: CAD file, 2022-12-17]
PCB/diptrace/3d models/button.step
7.40 x 11.0 x 11.0 mm
