himikat123/Weather-monitor-BIM32/enclosure/BME680 enclosure/SOLIDWORKS 2023/BME680_assembly.png

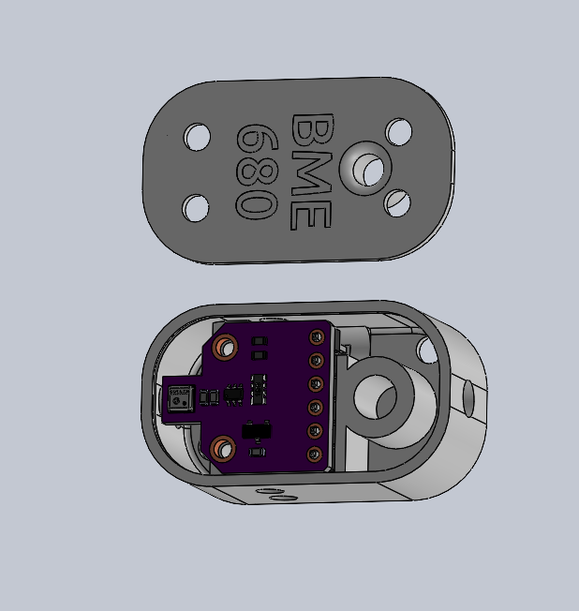
enclosure/BME680 enclosure/SOLIDWORKS 2023/BME680_assembly.png
