himikat123/Weather-monitor-BIM32/enclosure/Solidworks2023/assembly.png

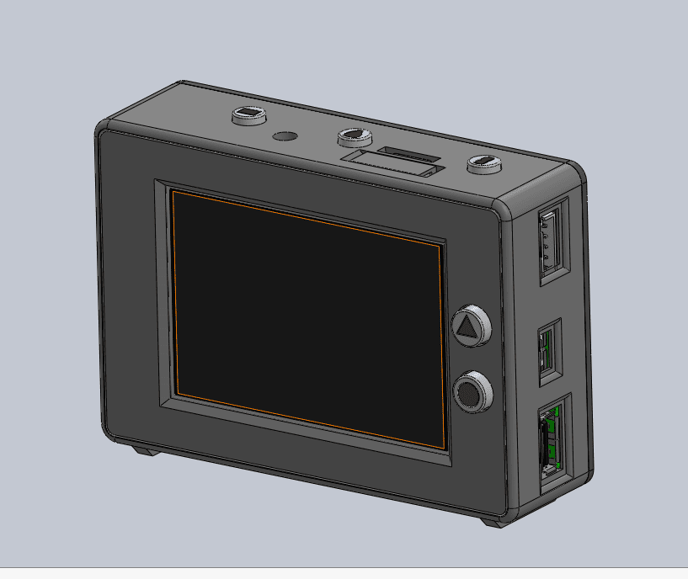
enclosure/Solidworks2023/assembly.png
