himikat123/Weather-monitor-BIM32/PCB/Assembled Bottom.png

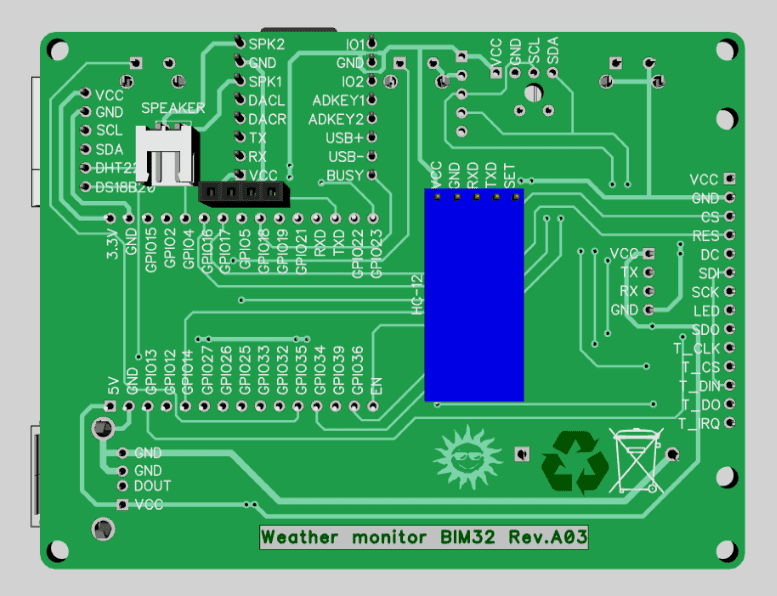
PCB/Assembled Bottom.png
