himikat123/Weather-monitor-BIM32/PCB/Assembled Top.png

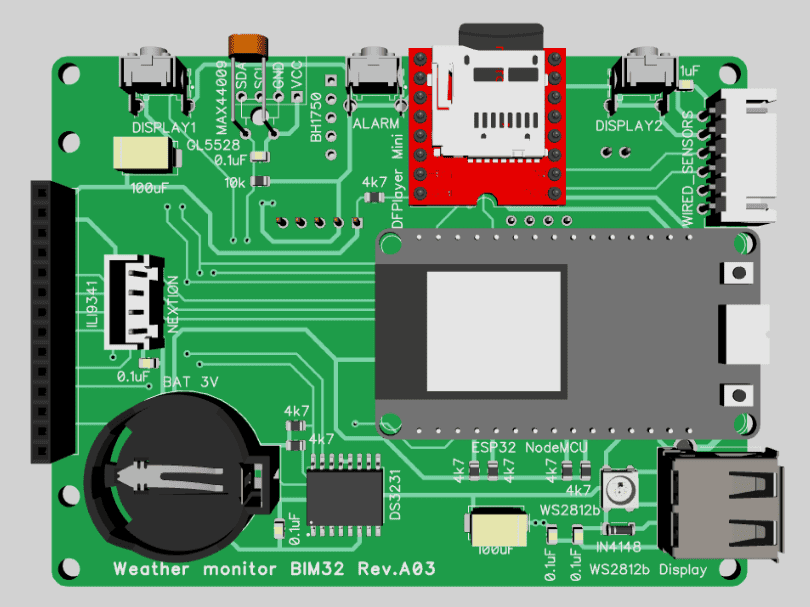
PCB/Assembled Top.png
