himikat123/Weather-monitor-BIM32/BIM32_Arduino/src/picturesIconsTiny.hpp

// array size is 1552
static const byte icon_tiny_01[] PROGMEM  = {
    0xff, 0xd8, 0xff, 0xe0, 0x00, 0x10, 0x4a, 0x46, 0x49, 0x46, 0x00, 0x01, 0x01, 0x01, 0x00, 0x48, 
    0x00, 0x48, 0x00, 0x00, 0xff, 0xdb, 0x00, 0x43, 0x00, 0x02, 0x01, 0x01, 0x02, 0x01, 0x01, 0x02, 
    0x02, 0x02, 0x02, 0x02, 0x02, 0x02, 0x02, 0x03, 0x05, 0x03, 0x03, 0x03, 0x03, 0x03, 0x06, 0x04, 
    0x04, 0x03, 0x05, 0x07, 0x06, 0x07, 0x07, 0x07, 0x06, 0x07, 0x07, 0x08, 0x09, 0x0b, 0x09, 0x08, 
    0x08, 0x0a, 0x08, 0x07, 0x07, 0x0a, 0x0d, 0x0a, 0x0a, 0x0b, 0x0c, 0x0c, 0x0c, 0x0c, 0x07, 0x09, 
    0x0e, 0x0f, 0x0d, 0x0c, 0x0e, 0x0b, 0x0c, 0x0c, 0x0c, 0xff, 0xdb, 0x00, 0x43, 0x01, 0x02, 0x02, 
    0x02, 0x03, 0x03, 0x03, 0x06, 0x03, 0x03, 0x06, 0x0c, 0x08, 0x07, 0x08, 0x0c, 0x0c, 0x0c, 0x0c, 
    0x0c, 0x0c, 0x0c, 0x0c, 0x0c, 0x0c, 0x0c, 0x0c, 0x0c, 0x0c, 0x0c, 0x0c, 0x0c, 0x0c, 0x0c, 0x0c, 
    0x0c, 0x0c, 0x0c, 0x0c, 0x0c, 0x0c, 0x0c, 0x0c, 0x0c, 0x0c, 0x0c, 0x0c, 0x0c, 0x0c, 0x0c, 0x0c, 
    0x0c, 0x0c, 0x0c, 0x0c, 0x0c, 0x0c, 0x0c, 0x0c, 0x0c, 0x0c, 0x0c, 0x0c, 0x0c, 0x0c, 0xff, 0xc0, 
    0x00, 0x11, 0x08, 0x00, 0x1e, 0x00, 0x1e, 0x03, 0x01, 0x22, 0x00, 0x02, 0x11, 0x01, 0x03, 0x11, 
    0x01, 0xff, 0xc4, 0x00, 0x1f, 0x00, 0x00, 0x01, 0x05, 0x01, 0x01, 0x01, 0x01, 0x01, 0x01, 0x00, 
    0x00, 0x00, 0x00, 0x00, 0x00, 0x00, 0x00, 0x01, 0x02, 0x03, 0x04, 0x05, 0x06, 0x07, 0x08, 0x09, 
    0x0a, 0x0b, 0xff, 0xc4, 0x00, 0xb5, 0x10, 0x00, 0x02, 0x01, 0x03, 0x03, 0x02, 0x04, 0x03, 0x05, 
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
    0xfa, 0xff, 0xda, 0x00, 0x0c, 0x03, 0x01, 0x00, 0x02, 0x11, 0x03, 0x11, 0x00, 0x3f, 0x00, 0xfc, 
    0x17, 0xd3, 0x3c, 0x3f, 0x7f, 0xa7, 0x5b, 0xc1, 0xaa, 0x5c, 0x59, 0x5f, 0xc7, 0xa5, 0x34, 0xbe, 
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
};
