himikat123/Weather-monitor-BIM32/BIM32_Arduino/src/picturesAnts.hpp

// array size is 11949
static const byte ant_acpoint[] PROGMEM = {
    0xff, 0xd8, 0xff, 0xe1, 0x04, 0x03, 0x45, 0x78, 0x69, 0x66, 0x00, 0x00, 0x4d, 0x4d, 0x00, 0x2a, 
    0x00, 0x00, 0x00, 0x08, 0x00, 0x07, 0x01, 0x12, 0x00, 0x03, 0x00, 0x00, 0x00, 0x01, 0x00, 0x01, 
    0x00, 0x00, 0x01, 0x1a, 0x00, 0x05, 0x00, 0x00, 0x00, 0x01, 0x00, 0x00, 0x00, 0x62, 0x01, 0x1b, 
    0x00, 0x05, 0x00, 0x00, 0x00, 0x01, 0x00, 0x00, 0x00, 0x6a, 0x01, 0x28, 0x00, 0x03, 0x00, 0x00, 
    0x00, 0x01, 0x00, 0x02, 0x00, 0x00, 0x01, 0x31, 0x00, 0x02, 0x00, 0x00, 0x00, 0x1f, 0x00, 0x00, 
    0x00, 0x72, 0x01, 0x32, 0x00, 0x02, 0x00, 0x00, 0x00, 0x14, 0x00, 0x00, 0x00, 0x91, 0x87, 0x69, 
    0x00, 0x04, 0x00, 0x00, 0x00, 0x01, 0x00, 0x00, 0x00, 0xa8, 0x00, 0x00, 0x00, 0xd4, 0x00, 0x12, 
    0x4f, 0x80, 0x00, 0x00, 0x27, 0x10, 0x00, 0x12, 0x4f, 0x80, 0x00, 0x00, 0x27, 0x10, 0x41, 0x64, 
    0x6f, 0x62, 0x65, 0x20, 0x50, 0x68, 0x6f, 0x74, 0x6f, 0x73, 0x68, 0x6f, 0x70, 0x20, 0x32, 0x34, 
    0x2e, 0x35, 0x20, 0x28, 0x57, 0x69, 0x6e, 0x64, 0x6f, 0x77, 0x73, 0x29, 0x00, 0x32, 0x30, 0x32, 
    0x33, 0x3a, 0x30, 0x37, 0x3a, 0x30, 0x31, 0x20, 0x32, 0x30, 0x3a, 0x32, 0x39, 0x3a, 0x33, 0x34, 
    0x00, 0x00, 0x00, 0x00, 0x00, 0x03, 0xa0, 0x01, 0x00, 0x03, 0x00, 0x00, 0x00, 0x01, 0x00, 0x01, 
    0x00, 0x00, 0xa0, 0x02, 0x00, 0x04, 0x00, 0x00, 0x00, 0x01, 0x00, 0x00, 0x00, 0x18, 0xa0, 0x03, 
    0x00, 0x04, 0x00, 0x00, 0x00, 0x01, 0x00, 0x00, 0x00, 0x18, 0x00, 0x00, 0x00, 0x00, 0x00, 0x00, 
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
    0x91, 0xa1, 0xb1, 0x42, 0x23, 0x24, 0x15, 0x52, 0xc1, 0x62, 0x33, 0x34, 0x72, 0x82, 0xd1, 0x43, 
    0x07, 0x25, 0x92, 0x53, 0xf0, 0xe1, 0xf1, 0x63, 0x73, 0x35, 0x16, 0xa2, 0xb2, 0x83, 0x26, 0x44, 
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
};
