himikat123/Weather-monitor-BIM32/BIM32_Arduino/src/sound.hpp

class Sound {
    public:
        void init(void);
        void volume(unsigned int vol);
        void equalizer(unsigned int eq);
        void play(unsigned int folder, unsigned int track);
        void stopPlaying(void);
        void hourlySignal(void);
        void alarm(void);
        void tempNotify(int tempLevel);
        void humNotify(int humLevel);
        void airNotify(unsigned int airLevel);

    private:
        bool _isAllowed();
        bool _hourlyCheck();
        void _playHourlySignal();
        void _reset();
        uint16_t _chckSum(uint8_t *sdata);
        void _sendCommand(uint8_t command, uint8_t hByte, uint8_t lByte);

        unsigned int _alarm_rang = 60;
        unsigned int _hourly_rang = 0;
        int _prevTempLevel = TEMP_COMFORTABLE;
        int _prevHumLevel = HUM_COMFORTABLE;
        unsigned int _prevAirLevel = AIR_CLEAN;
        boolean _mp3_found = false;
};

/**
 * DF player initialization
 */
void Sound::init(void) {
    Serial.println(SEPARATOR);
    Serial.println("Initialize DF Player...");

    if(digitalRead(MP3_BUSY_PIN)) {
        time_t mils = millis();
        _reset();
        while(1) { 
            if(!global.mp3_busy) {
                global.mp3_busy = true;
                _mp3_found = true;
                break;
            }
            if(millis() - mils > 2000) break;
        }
    }
    Serial.printf("DFPlayer %sfound\r\n", _mp3_found ? "" : "NOT ");
}

/**
 * Change voilume
 */
void Sound::volume(unsigned int vol) {
    if(vol <= 30) _sendCommand(0x06, 0x00, vol);
}

/**
 * Change equalizer
 */
void Sound::equalizer(unsigned int eq) {
    if(eq <= 5) _sendCommand(0x07, 0x00, eq);
}

/**
 * Play a track
 * @param folder number
 * @param track number
 */
void Sound::play(unsigned int folder, unsigned int track) {
    equalizer(config.sound_eq());
    vTaskDelay(100);
    volume(config.sound_vol());
    vTaskDelay(100);

    if(folder==2 and track<=20) {
        folder = 6;
        track++;
    }
    if(folder==1 and track<=33) {
        if(String(config.lang()) == "de") folder = 2;
        else if(String(config.lang()) == "ru") folder = 3;
        else if(String(config.lang()) == "pl") folder = 4;
        else if(String(config.lang()) == "ua") folder = 5;
        if(track == 0) track = 24;
    }
    for(uint8_t i=0; i<5; i++) {
        _sendCommand(0x0F, folder, track);
        time_t mils = millis();
        while(1) {
            if(!digitalRead(MP3_BUSY_PIN)) {
                i = 5;
                break;
            }
            if(millis() - mils > 10000) {
                _reset();
                vTaskDelay(1000);
                break;
            }
        }
    }
}

/**
 * Stop playing
 */
void Sound::stopPlaying(void) {
    _sendCommand(0x16, 0x00, 0x00);
}

/**
 * Check if sound is allowed
 */
bool Sound::_isAllowed() {
    if(_mp3_found and digitalRead(MP3_BUSY_PIN)) {
        switch(config.sound_hourly()) {
            case 0: return true;
            case 2: if(weather.get_isDay()) return true;
            case 3: return _hourlyCheck();
            default: return false;
        }
    }
    return false;
}

bool Sound::_hourlyCheck() {
    uint8_t fromH = config.sound_hour_from();
    uint8_t toH = config.sound_hour_to();
    if(fromH < toH) {
        if(fromH <= hour() && hour() < toH) return true;
    }
    else {
        if(hour() >= fromH || hour() < toH) return true;
    }
    return false;
}

/** 
 * Check if it is time to play hourly signal and playing
 */
void Sound::hourlySignal() {
    if(minute() == 0 and _hourly_rang != hour()) {
        _playHourlySignal();
    }
}

/** 
 * Playing an hourly sound and speaking the time every hour
 */
void Sound::_playHourlySignal() {
    if(_isAllowed()) {
        _hourly_rang = hour();
        play(1, hour());
    }
}

/** 
 * Check if it's time to ring the alarm
 */
void Sound::alarm() {
    if(_mp3_found) {
        for(int i=0; i<ALARMS; i++) {
            if(config.alarm_state(i) and config.alarm_weekday(i, weekday() == 1 ? 6 : weekday() - 2)) {
                if(config.alarm_time(i, 0) == hour() and config.alarm_time(i, 1) == minute() and _alarm_rang != minute()) { 
                    play(2, config.alarm_melodie(i));
                    _alarm_rang = minute();
                }
            }
        }
        if(minute() == 0 and second() >= 0 and second() <= 5) _alarm_rang = 60;

        // Stop alarm ringing if the alarm button was pressed
        if(global.alarm_but_pressed) {
            stopPlaying();
            global.alarm_but_pressed = false;
        }
    }
}

void Sound::tempNotify(int tempLevel) {
    if(_isAllowed()) {
        if(_prevTempLevel != tempLevel) {
            _prevTempLevel = tempLevel;
            switch(tempLevel) {
                case TEMP_COMFORTABLE: play(1, 25); break;
                case TEMP_TOO_COLD: play(1, 26); break;
                case TEMP_TOO_HOT: play(1, 27); break;
                default: ; break;
            }
        }
    }
}

void Sound::humNotify(int humLevel) {
    if(_isAllowed()) {
        if(_prevHumLevel != humLevel) {
            _prevHumLevel = humLevel;
            switch(humLevel) {
                case HUM_COMFORTABLE: play(1, 28); break;
                case HUM_TOO_DRY: play(1, 29); break;
                case HUM_TOO_HUMID: play(1, 30); break;
                default: ; break;
            }
        }
    }
}

void Sound::airNotify(unsigned int airLevel) {
    if(_isAllowed()) {
        if(_prevAirLevel != airLevel) {
            _prevAirLevel = airLevel;
            switch(airLevel) {
                case AIR_CLEAN: play(1, 31); break;
                case AIR_POLLUTED: play(1, 32); break;
                case AIR_HEAVILY_POLLUTED: play(1, 33); break;
                default: ; break;
            }
        }
    }
}

void Sound::_reset() {
    _sendCommand(0x0C, 0x00, 0x00);
    _sendCommand(0x09, 0x00, 0x02);
    vTaskDelay(200);
    equalizer(config.sound_eq());
    vTaskDelay(100);
    volume(config.sound_vol());
    vTaskDelay(100);
}

uint16_t Sound::_chckSum(uint8_t *sdata) {
    uint16_t sum = 0;
    for(int i=1; i<7; i++) {
        sum += sdata[i];
    }
    return -sum;
}

void Sound::_sendCommand(uint8_t command, uint8_t hByte, uint8_t lByte) {
    uint8_t sdata[10] = {0x7E, 0xFF, 0x06, command, 0x00, hByte, lByte, 0x00, 0x00, 0xEF};
    uint16_t sum = _chckSum(sdata);
    sdata[7] = (uint8_t)(sum >> 8);
    sdata[8] = (uint8_t)(sum);
    if(global.uart2_tx != DFPlayer) {
        Serial2.setPins(HC12_RX_PIN, MP3_TX_PIN);
        global.uart2_tx = DFPlayer;
    }
    Serial2.write(sdata, 10);
    Serial2.flush();
}
